AmitParan/smart-boiler/Matlab/figures/energy_philosophy.png

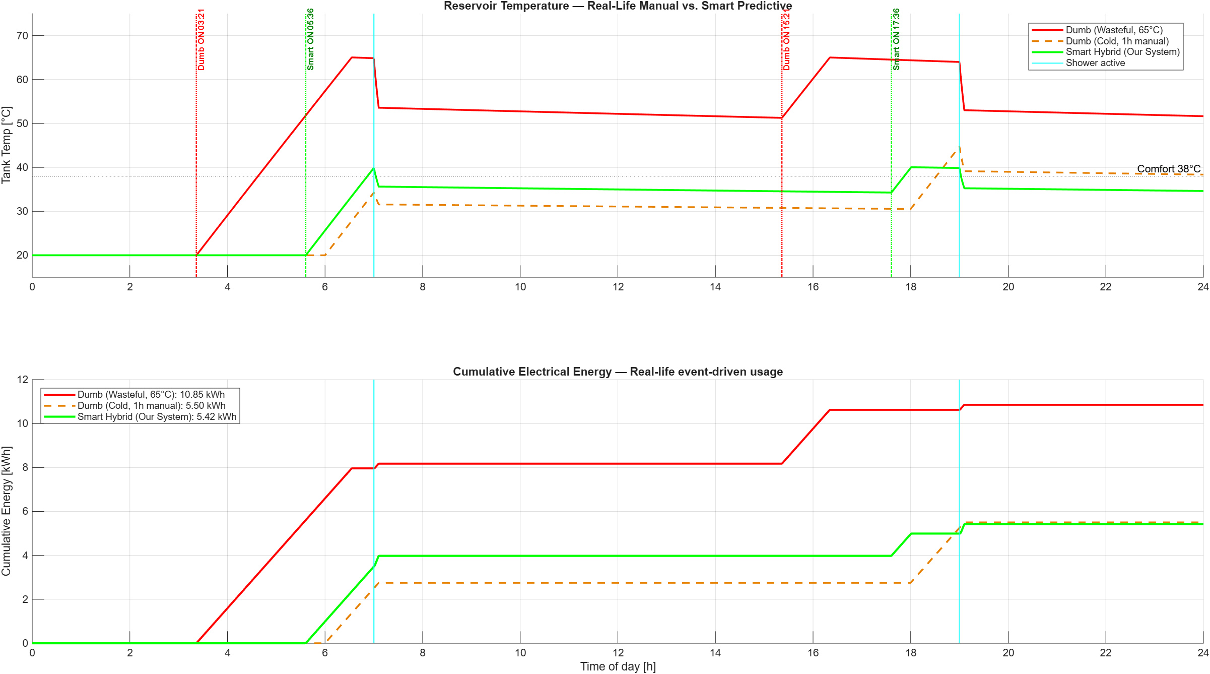
Matlab/figures/energy_philosophy.png
