AmitParan/smart-boiler/Matlab/figures/energy_stacked_breakdown.png

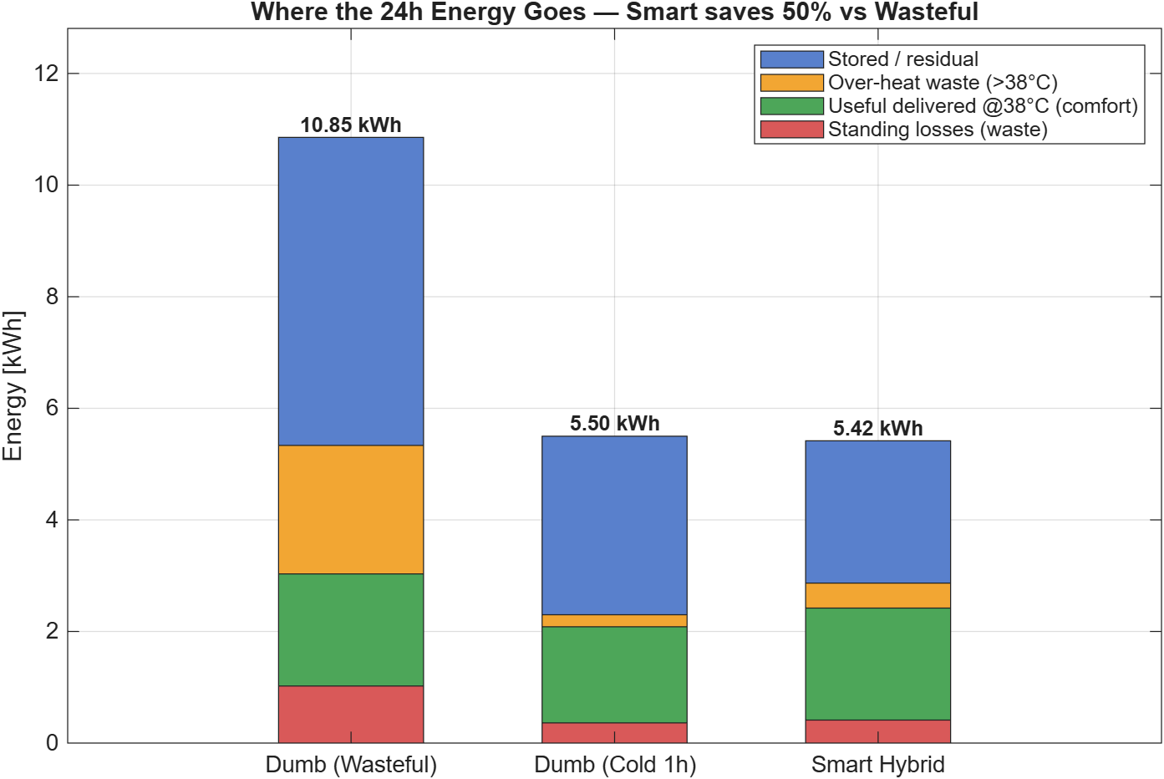
Matlab/figures/energy_stacked_breakdown.png
