AmitParan/smart-boiler/Matlab/figures/Scenario_1_Preheating.png

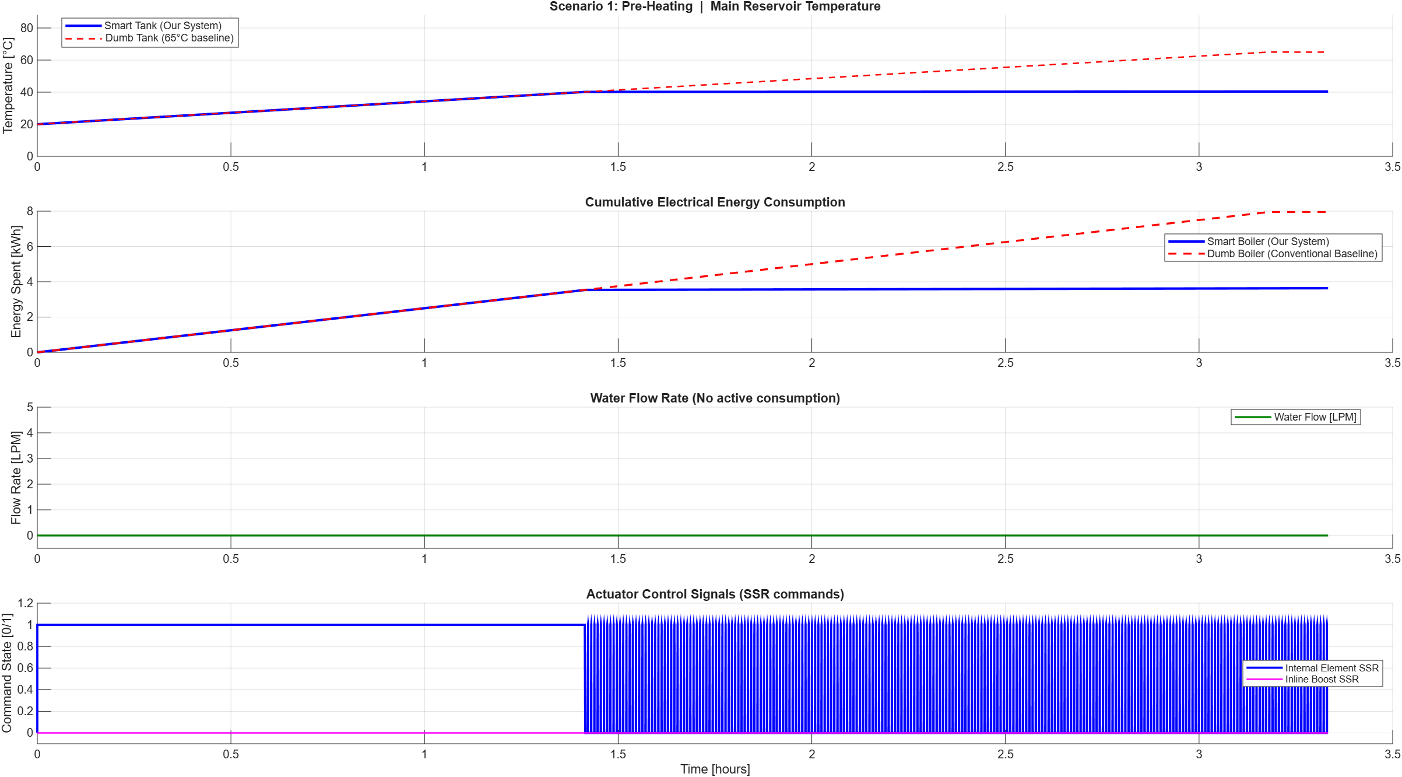
Matlab/figures/Scenario_1_Preheating.png
