AmitParan/smart-boiler/Matlab/figures/Scenario_2_ColdShowerStart.png

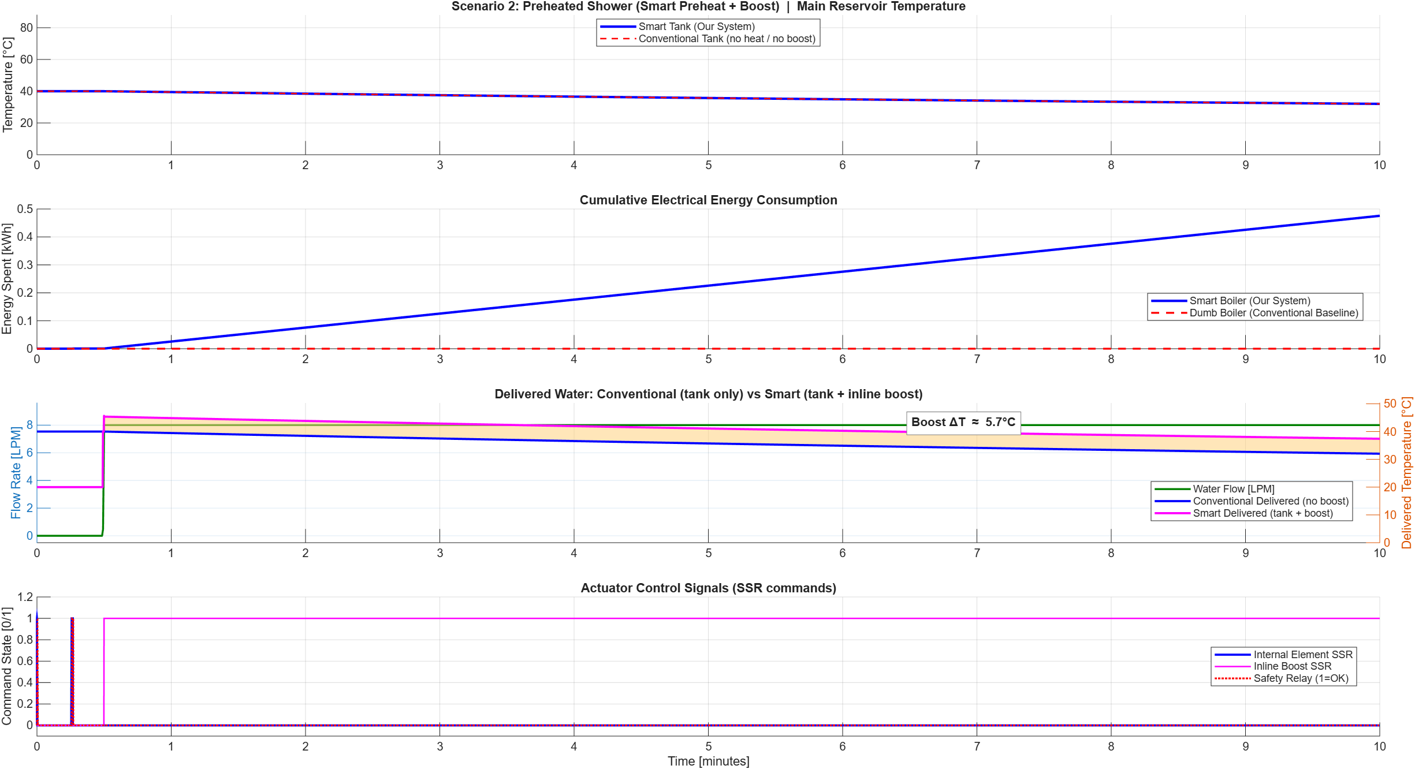
Matlab/figures/Scenario_2_ColdShowerStart.png
