AmitParan/smart-boiler/Matlab/figures/Scenario_5_SolarBypass.png

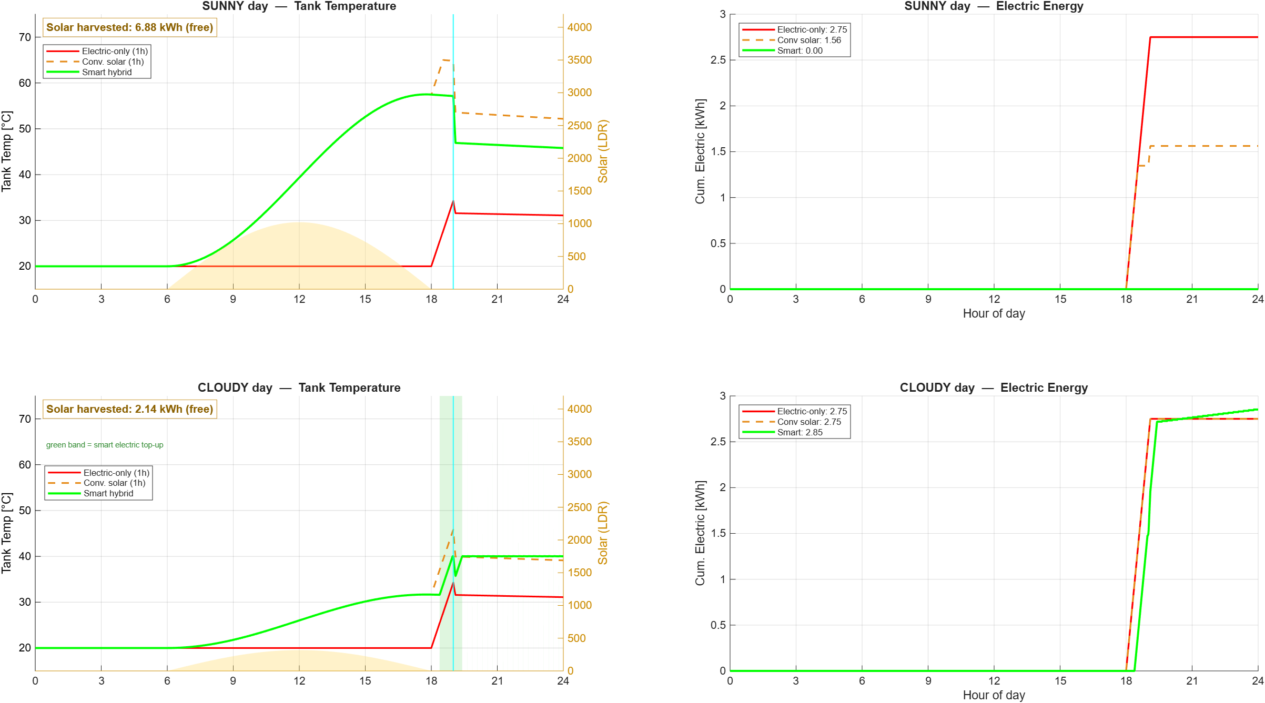
Matlab/figures/Scenario_5_SolarBypass.png
