AmitParan/smart-boiler/Matlab/figures/Scenario_6_PLC_CommLoss.png

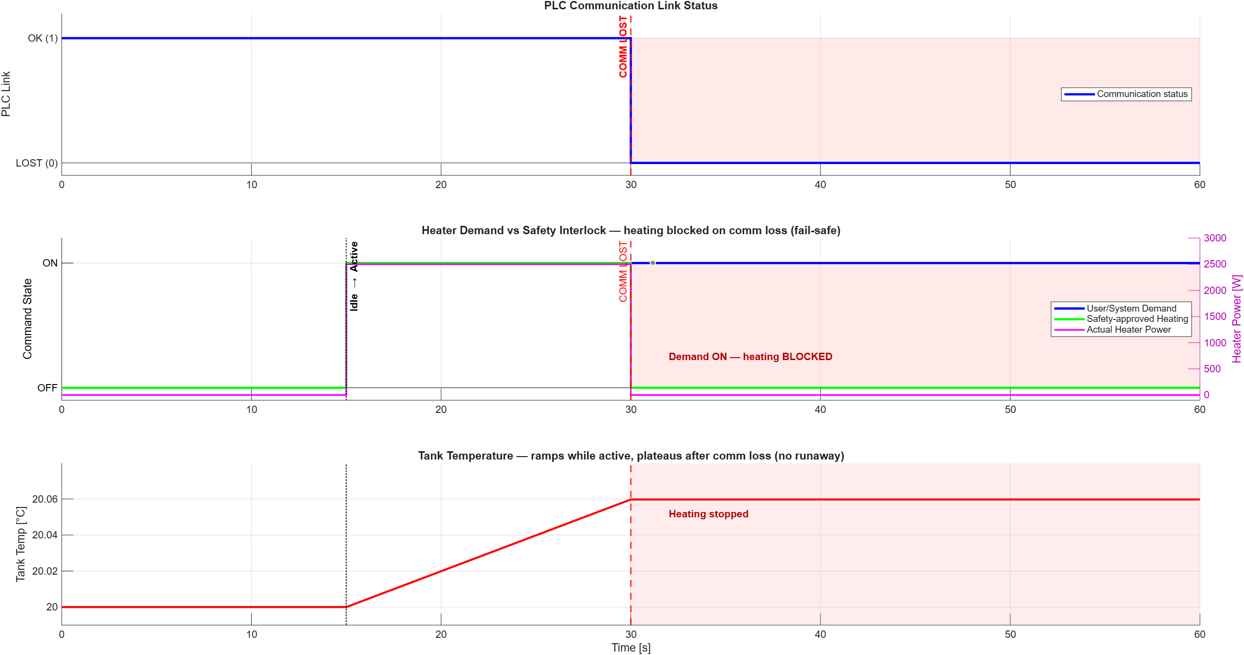
Matlab/figures/Scenario_6_PLC_CommLoss.png
