AmitParan/smart-boiler/slave/src/tasks/current_task.cpp

#include "current_task.h"
#include "config.h"
#include "shared_data.h"
#include "system_mode.h"
#include <Arduino.h>

static const int numSamples = 100;

void TaskCurrent(void * pvParameters) {
    // Initialize pin as analog first, then set attenuation
    analogReadResolution(12);
    analogRead(PIN_CURRENT_SENSOR);                              // primes the pin
    analogSetPinAttenuation(PIN_CURRENT_SENSOR, ADC_11db);

    // -----------------------------------------------------------------------
    //  Zero-current calibration
    //  SSRs are off at boot — average 200 samples to find the actual quiescent
    //  voltage of this specific sensor (ACS758 tolerance ±1% on VREF).
    // -----------------------------------------------------------------------
    Serial.println("[CURRENT] Calibrating zero reference...");
    float vref_sum = 0;
    for (int i = 0; i < 200; i++) {
        float v_adc = (analogRead(PIN_CURRENT_SENSOR) / 4095.0f) * 3.3f;
        vref_sum += v_adc / CURRENT_DIVIDER_RATIO;
        vTaskDelay(pdMS_TO_TICKS(5));
    }
    float vref_actual = vref_sum / 200.0f;

    // Derive actual VCC from measured VREF (ACS758: VREF = VCC/2)
    float vcc_actual = vref_actual * 2.0f;
    // Sensitivity scales linearly with VCC (spec is 40mV/A at 5V)
    float sensitivity_actual = ACS758_SENSITIVITY * (vcc_actual / 5.0f);

    Serial.printf("[CURRENT] Calibrated VREF = %.3fV (expected %.3fV)\n",
                  vref_actual, ACS758_VREF);
    Serial.printf("[CURRENT] VCC = %.3fV  sensitivity = %.1f mV/A (nominal 40.0)\n",
                  vcc_actual, sensitivity_actual * 1000.0f);

    // Validate VREF within ±10% of nominal 2.5V
    // If out of range the sensor is mis-powered — disable uncommanded-current check
    const float VREF_MIN = ACS758_VREF * 0.90f;  // 2.25V
    const float VREF_MAX = ACS758_VREF * 1.10f;  // 2.75V
    if (vref_actual >= VREF_MIN && vref_actual <= VREF_MAX) {
        current_sensor_valid = true;
        Serial.println("[CURRENT] Sensor OK — uncommanded-current check ENABLED");
    } else {
        current_sensor_valid = false;
        Serial.printf("[CURRENT] WARN: VREF out of range (%.3fV). Sensor mis-powered? Uncommanded-current check DISABLED.\n",
                      vref_actual);
    }
    Serial.println("[CURRENT] Task started");

    for(;;) {
        if (currentMode == MODE_DEMO) {
            // Compute mock RMS current from commanded SSR state
            uint8_t local_pwm_int = 0u, local_pwm_bst = 0u;
            if (xSemaphoreTake(guard_cmd, pdMS_TO_TICKS(10)) == pdTRUE) {
                local_pwm_int = cmd_pwm_internal;
                local_pwm_bst = cmd_pwm_boost;
                xSemaphoreGive(guard_cmd);
            }
            float mock_rms;
            if (slave_demo_fault_sim) {
                // Scenario 8: simulate stuck triac - report load even with cmds=0
                mock_rms = 13.64f;  // 3000W / 220V
            } else if (local_pwm_bst > 0u) {
                mock_rms = 13.64f;  // SSR BOOST (external) = 3000W / 220V
            } else if (local_pwm_int > 0u) {
                mock_rms = 11.36f;  // SSR INT (internal)   = 2500W / 220V
            } else {
                mock_rms = 0.0f;
            }
            if (xSemaphoreTake(guard_current, pdMS_TO_TICKS(10)) == pdTRUE) {
                current_rms = mock_rms;
                power_watts = mock_rms * 220.0f;
                xSemaphoreGive(guard_current);
            }
            vTaskDelay(pdMS_TO_TICKS(500));
            continue;
        }

        float sumSq = 0;

        // Sample the ADC to capture AC waveform (50 Hz)
        for (int i = 0; i < numSamples; i++) {
            float v_adc = (analogRead(PIN_CURRENT_SENSOR) / 4095.0f) * 3.3f;
            float v_sensor = v_adc / CURRENT_DIVIDER_RATIO;
            float current_instant = (v_sensor - vref_actual) / sensitivity_actual;
            sumSq += (current_instant * current_instant);
            vTaskDelay(pdMS_TO_TICKS(1));
        }

        float rms_current = sqrtf(sumSq / numSamples);

        // Filter noise floor
        if (rms_current < 0.2f) rms_current = 0.0f;

        if (xSemaphoreTake(guard_current, pdMS_TO_TICKS(10)) == pdTRUE) {
            current_rms = rms_current;
            power_watts = rms_current * 220.0f;
            xSemaphoreGive(guard_current);
        }

        vTaskDelay(pdMS_TO_TICKS(500));
    }
}
