AmitParan/smart-boiler/slave/src/core/shared_data.cpp

#include "shared_data.h"

// Sensor readings
float temps[3]       = {0.0f, 0.0f, 0.0f};
float current_flow   = 0.0f;
float current_rms    = 0.0f;
float power_watts    = 0.0f;

// SSR state flags
volatile bool    internal_ssr_on  = false;
volatile bool    boost_ssr_on     = false;

// Commands from master
volatile uint8_t cmd_pwm_internal = 0u;
volatile uint8_t cmd_pwm_boost    = 0u;
volatile uint8_t cmd_flags        = 0u;

// Safety
volatile bool    system_fault     = false;

// FreeRTOS mutexes (created in main.cpp setup(), before tasks start)
SemaphoreHandle_t guard_temps   = nullptr;
SemaphoreHandle_t guard_flow    = nullptr;
SemaphoreHandle_t guard_current = nullptr;
SemaphoreHandle_t guard_cmd     = nullptr;

// Demo mode flag-based sensor injection
volatile bool     slave_demo_flow_active = false;
volatile bool     slave_demo_overtemp    = false;
volatile bool     slave_demo_fault_sim   = false;

// PLC watchdog
volatile uint32_t last_cmd_received_ms = 0u;
volatile bool     cmd_ever_received    = false;
volatile bool     current_sensor_valid = false;  // set true only when VREF is in spec

// Temperature sensor health (REALTIME only) - see shared_data.h
volatile bool     temp_sensors_valid   = false;
volatile bool     temp_ever_read       = false;  // no REALTIME read attempted yet

// Spinlock for flow pulse counter ISR
portMUX_TYPE timerMux = portMUX_INITIALIZER_UNLOCKED;
