AmitParan/smart-boiler/slave/src/comms/plc_task.cpp

#include "plc_task.h"
#include "plc_comms.h"
#include "link.h"
#include "config.h"
#include <Arduino.h>

// ---------------------------------------------------------------------------
//  TaskPLC — triggered STATUS response + 5s heartbeat
//
//  Protocol (half-duplex KQ-330 — only one device transmits at a time):
//    1. Poll Serial1 every 10ms for incoming CMD from master
//    2. When CMD received: wait 200ms guard time, then push STATUS
//    3. Heartbeat: if no CMD received for 5s, push STATUS anyway so the
//       master knows the slave is alive
//
//  Why triggered instead of periodic unconditional push?
//  The KQ-330 is half-duplex. Master sends CMD every ~1s and listens for
//  STATUS for 3s. If slave also pushes every 1s independently, the two
//  transmissions collide on the power line and both packets are lost.
//  Triggered response guarantees the channel is quiet before slave TX.
// ---------------------------------------------------------------------------
void TaskPLC(void* pvParameters) {
    PLC_Init();
    Serial.printf("[COMMS] Task started over %s — triggered STATUS response\n",
                  link_name());

    uint32_t last_status_ms = millis();

    for (;;) {
        bool cmd_received = PLC_ReceivePacket();

        if (cmd_received) {
#ifndef LINK_WIFI
            // -----------------------------------------------------------------
            //  KQ-330 GUARD TIME — DO NOT CHANGE (PLC transport only)
            //  200ms is required between CMD receipt and STATUS transmission.
            //  This allows the KQ-330 power line carrier from the master's CMD
            //  to fully settle before the slave begins transmitting STATUS.
            //  Tested and verified at 200ms. Shorter values cause collisions.
            //
            //  WiFi needs none of this: UDP is full-duplex and there is no
            //  shared carrier to settle, so we answer immediately.
            // -----------------------------------------------------------------
            static const uint16_t KQ330_GUARD_TIME_MS = 200u;
            vTaskDelay(pdMS_TO_TICKS(KQ330_GUARD_TIME_MS));
#endif
            PLC_SendStatus();
            last_status_ms = millis();
        }

        // Heartbeat: push STATUS if master has been silent for 5 seconds
        if (millis() - last_status_ms >= 5000UL) {
            PLC_SendStatus();
            last_status_ms = millis();
        }

        vTaskDelay(pdMS_TO_TICKS(10));
    }
}
