AmitParan/smart-boiler/master/src/control/app_mode.h

#ifndef APP_MODE_H
#define APP_MODE_H

#include <Arduino.h>

// ---------------------------------------------------------------------------
//  AppMode — runtime operation mode (toggled from the Settings screen)
//
//  MODE_DEMO      : Master injects scripted sensor values into SystemManager.
//                       PLC is still active — slave receives real CMD packets
//                       and fires SSRs accordingly. Use this to demonstrate
//                       system behaviour or run automated test scenarios.
//
//  MODE_REALTIME  : Master uses actual sensor readings from slave STATUS
//                       packets. Normal production operation.
// ---------------------------------------------------------------------------
enum AppMode : uint8_t {
    MODE_DEMO     = 0,   ///< Automated scenarios; mock sensor data injected by master
    MODE_REALTIME = 1,   ///< Production; real sensors from slave STATUS packets
};

extern volatile AppMode appMode;

// ---------------------------------------------------------------------------
//  Demo mode injected values
//  Written by the demo scenario task, read by sendCommand() in comms_master.cpp.
// ---------------------------------------------------------------------------
extern volatile float demo_temp;    ///< tank temperature [°C]
extern volatile float demo_flow;    ///< flow rate [L/min]
extern volatile bool  demo_ui_on;   ///< boiler ON/OFF button state
extern volatile bool  demo_stop_comms;  ///< when true TaskMasterComms suppresses TX (scenario 6)
extern volatile bool  demo_fault_sim;   ///< when true slave simulates stuck-SSR current (scenario 8)
extern volatile bool  demo_solar_active; ///< when true scenario 5 solar sweep is running (changes log label)
#endif // APP_MODE_H
