AmitParan/smart-boiler/master/src/ui/ui_manager.cpp

// ui_manager.cpp  — Multi-screen consumer redesign (v6)
// Screen: 800 x 480  |  LVGL v8  |  Montserrat fonts
// Layout/flow ported from docs/ui-mockup/index.html

#include "ui_manager.h"
#include <Arduino.h>
#include "app_mode.h"
#include <WiFi.h>
#include <HTTPClient.h>
#include <ArduinoJson.h>
#include <esp_display_panel.hpp>
#include <lvgl.h>
#include <time.h>
#include "lvgl_v8_port.h"
#include "config.h"
#include "DataManager.h"

#define WEATHER_API_KEY      "7a1028898a2cdcc08a58a8109fb061e4"  // local only - do not commit
#define WEATHER_CITY         "Tel%20Aviv"  // URL-encoded space; a literal space breaks the request
#define WEATHER_COUNTRY_CODE "IL"
#define SETUP_AP_SSID        "Boiler-Setup"

using namespace esp_panel::drivers;
using namespace esp_panel::board;

// ---------------------------------------------------------------------------
//  Colour palette
// ---------------------------------------------------------------------------
#define CLR_BG       lv_color_hex(0xF0F4F8)  // light grey background
#define CLR_TOPBAR   lv_color_hex(0x1565C0)  // deep blue top bar / headers
#define CLR_ACCENT   lv_color_hex(0x1565C0)  // accent (buttons, ring)
#define CLR_ON       lv_color_hex(0x2E7D32)  // boiler ON  — green
#define CLR_OFF      lv_color_hex(0xC62828)  // boiler OFF — red
#define CLR_TEXT     lv_color_hex(0x1A1A2E)  // primary text
#define CLR_SUBTEXT  lv_color_hex(0x7B8794)  // secondary text
#define CLR_READY    lv_color_hex(0x2E7D32)  // shower ready
#define CLR_WAITING  lv_color_hex(0xE65100)  // shower not ready
#define CLR_BORDER   lv_color_hex(0xE0E0E0)  // card border
#define CLR_DIAG_BG  lv_color_hex(0x263238)  // diagnostics card background
#define CLR_DIAG_HDR lv_color_hex(0x37474F)  // diagnostics header background

static const int LEAD_TIME_MIN = 45;  // typical lead for the on-screen estimate only; the real lead is adaptive (smart_preheat.cpp)

// ---------------------------------------------------------------------------
//  Page containers (each 800x480, shown/hidden — only one visible at a time)
// ---------------------------------------------------------------------------
static lv_obj_t* page_home        = NULL;
static lv_obj_t* page_settings     = NULL;
static lv_obj_t* btn_app_mode      = NULL;  // Data-source (Demo/Real-time) button — Diagnostics header
static lv_obj_t* lbl_app_mode      = NULL;  // Data-source (Demo/Real-time) label — Diagnostics header
static lv_obj_t* page_schedule     = NULL;
static lv_obj_t* page_network      = NULL;
static lv_obj_t* page_password     = NULL;
static lv_obj_t* page_stats        = NULL;
static lv_obj_t* page_diagnostics  = NULL;
static lv_obj_t* page_solar        = NULL;
static lv_obj_t* page_wizard       = NULL;

// ---------------------------------------------------------------------------
//  Widget pointers — Home
// ---------------------------------------------------------------------------
lv_obj_t* lbl_water_temp     = NULL;
static lv_obj_t* lbl_target_inline = NULL;     // "Target 60°" inside the circle
lv_obj_t* lbl_time           = NULL;
lv_obj_t* lbl_date           = NULL;
lv_obj_t* btn_power          = NULL;
lv_obj_t* lbl_power_status   = NULL;
lv_obj_t* led_heating        = NULL;
lv_obj_t* lbl_wifi_icon      = NULL;
lv_obj_t* lbl_weather_icon   = NULL;
lv_obj_t* lbl_weather_temp   = NULL;
static lv_obj_t* temp_circle_obj      = NULL;
static lv_obj_t* lbl_shower_readiness = NULL;
static lv_obj_t* btn_auto_badge       = NULL;
static lv_obj_t* lbl_auto_badge       = NULL;

// Kept for header API compatibility
lv_obj_t* lbl_target_temp  = NULL;
lv_obj_t* btn_timer        = NULL;   // unused
lv_obj_t* lbl_timer_status = NULL;   // unused
lv_obj_t* btn_temp_up      = NULL;
lv_obj_t* btn_temp_down    = NULL;
lv_obj_t* lbl_boost_temp   = NULL;   // unused (no longer surfaced to consumer view)
lv_obj_t* lbl_flow_rate    = NULL;   // unused
lv_obj_t* lbl_showers      = NULL;   // unused
lv_obj_t* lbl_wait_time    = NULL;   // unused
lv_obj_t* lbl_system_mode  = NULL;   // shown on Stats page
lv_obj_t* led_ssr_internal = NULL;   // unused
lv_obj_t* led_ssr_boost    = NULL;   // unused

// ---------------------------------------------------------------------------
//  Widget pointers — Network / Password
// ---------------------------------------------------------------------------
static lv_obj_t* net_list_container = NULL;
static lv_obj_t* lbl_net_status     = NULL;
static lv_obj_t* lbl_pwd_title      = NULL;
static lv_obj_t* lbl_pwd_error      = NULL;
static lv_obj_t* password_textarea  = NULL;
static lv_obj_t* keyboard           = NULL;
static lv_obj_t* lbl_eye_icon       = NULL;
static lv_obj_t* btn_connect        = NULL;
static lv_obj_t* lbl_connect_btn_text = NULL;
static lv_obj_t* save_modal         = NULL;
static lv_obj_t* lbl_save_modal_ssid = NULL;

// ---------------------------------------------------------------------------
//  Widget pointers — Schedule
// ---------------------------------------------------------------------------
static lv_obj_t* sched_body         = NULL;
static lv_obj_t* btn_mode_manual    = NULL;
static lv_obj_t* lbl_mode_manual    = NULL;
static lv_obj_t* btn_mode_smart     = NULL;
static lv_obj_t* lbl_mode_smart     = NULL;
static lv_obj_t* btn_mode_ready     = NULL;
static lv_obj_t* lbl_mode_ready     = NULL;
static lv_obj_t* panel_ready        = NULL;
static lv_obj_t* panel_smart        = NULL;
static lv_obj_t* panel_manual       = NULL;
static lv_obj_t* sched_right_col    = NULL;
static lv_obj_t* btn_day_wk         = NULL;
static lv_obj_t* lbl_day_wk         = NULL;
static lv_obj_t* btn_day_we         = NULL;
static lv_obj_t* lbl_day_we         = NULL;
static lv_obj_t* btn_slot_am        = NULL;
static lv_obj_t* lbl_slot_am        = NULL;
static lv_obj_t* btn_slot_pm        = NULL;
static lv_obj_t* lbl_slot_pm        = NULL;
static lv_obj_t* btn_slot_en        = NULL;
static lv_obj_t* lbl_slot_en        = NULL;
static lv_obj_t* lbl_hh             = NULL;
static lv_obj_t* lbl_mm             = NULL;
static lv_obj_t* lbl_next_preheat   = NULL;
static lv_obj_t* lbl_skip_btn       = NULL;

// ---------------------------------------------------------------------------
//  Widget pointers — Setup Wizard (first-time preferences, Settings-triggered)
// ---------------------------------------------------------------------------
static lv_obj_t* wiz_step_temp      = NULL;
static lv_obj_t* wiz_step_household = NULL;
static lv_obj_t* wiz_step_schedule  = NULL;
static lv_obj_t* lbl_wiz_progress   = NULL;
static lv_obj_t* lbl_wiz_temp       = NULL;
static lv_obj_t* lbl_wiz_household  = NULL;
static lv_obj_t* lbl_wiz_hh         = NULL;
static lv_obj_t* lbl_wiz_mm         = NULL;
static lv_obj_t* btn_wiz_back       = NULL;
static lv_obj_t* btn_wiz_next       = NULL;
static lv_obj_t* lbl_wiz_next_text  = NULL;

// ---------------------------------------------------------------------------
//  Widget pointers — Stats (live status) / Diagnostics
// ---------------------------------------------------------------------------
static lv_obj_t* lbl_stat_power = NULL;
static lv_obj_t* lbl_stat_flow  = NULL;
static lv_obj_t* lbl_stat_plc   = NULL;
static lv_obj_t* lbl_usage_today = NULL;
static lv_obj_t* chart_usage     = NULL;
static lv_chart_series_t* ser_usage = NULL;

// ---------------------------------------------------------------------------
//  Widget pointers — Solar forecast page
// ---------------------------------------------------------------------------
static lv_obj_t* lbl_solar_peak  = NULL;
static lv_obj_t* chart_solar     = NULL;
static lv_chart_series_t* ser_solar = NULL;

static lv_obj_t* lbl_diag_tint   = NULL;
static lv_obj_t* lbl_diag_tboost = NULL;
static lv_obj_t* lbl_diag_flow   = NULL;
static lv_obj_t* lbl_diag_power  = NULL;
static lv_obj_t* lbl_diag_plc    = NULL;
static lv_obj_t* lbl_diag_heater_int   = NULL;
static lv_obj_t* lbl_diag_heater_boost = NULL;
static lv_obj_t* lbl_diag_rssi   = NULL;
static lv_obj_t* lbl_diag_heap   = NULL;
static lv_obj_t* lbl_diag_uptime = NULL;

// ---------------------------------------------------------------------------
//  Screensaver
// ---------------------------------------------------------------------------
static lv_obj_t* screensaver      = NULL;
static lv_obj_t* screensaver_time = NULL;
static lv_obj_t* screensaver_date = NULL;
unsigned long last_touch_time = 0;
#define SCREENSAVER_TIMEOUT 60000

// ---------------------------------------------------------------------------
//  State
// ---------------------------------------------------------------------------
bool   boiler_state       = false;
bool   timer_enabled      = false;
int    target_temperature = 60;
bool   wifi_connected     = false;
char   selected_network[64] = "";
String scanned_networks[20];
int    scanned_rssi[20];
int    num_networks         = 0;
unsigned long last_weather_update = 0;

// Water usage tracking (Stats page) — 24 hourly buckets, reset at midnight,
// persisted to flash so a reboot doesn't lose today's progress.
#define USAGE_HOURS 24
static float g_hourly_liters[USAGE_HOURS] = {0};
static float g_hourly_temp[USAGE_HOURS]   = {0};
static int   g_usage_day             = -1;   // day-of-year; -1 = not loaded yet
static unsigned long g_last_usage_ms      = 0;
static unsigned long g_last_usage_save_ms = 0;

// Schedule — operation-mode + ready-by state. Drives the SmartPreheat brain
// (smart_preheat.cpp) via UI_GetOpMode() / UI_GetReadyByMinutes().
static bool g_auto_enabled  = true;
static bool g_smart_learn   = false;   // false = "Ready by" mode
// Ready-by schedule: [day-type][slot]. day 0=weekday 1=weekend, slot 0=morning 1=evening.
static int  g_ready_hh[2][2] = {{7, 19}, {9, 19}};
static int  g_ready_mm[2][2] = {{0, 0},  {0, 0}};
static bool g_ready_en[2][2] = {{true, false}, {true, false}};  // is this slot active?
static int  g_sched_day_idx  = 0;   // which day-type is being edited (0=weekday 1=weekend)
static int  g_sched_slot_idx = 0;   // which slot is being edited   (0=morning 1=evening)
static bool g_skip_today     = false;

// Setup Wizard — working values for the in-progress step, plus the last
// persisted household/ready-time preferences (loaded at boot, used to
// prefill the wizard next time it's opened). target_temperature doubles
// as both the live value and the persisted preference, so it isn't
// duplicated here.
static int  wizard_step      = 0;   // 0..2
static int  wiz_temp         = 60;
static int  wiz_household    = 2;
static int  wiz_ready_hh     = 7;
static int  wiz_ready_mm     = 0;
static int  g_pref_household = 2;
static int  g_pref_ready_hh  = 7;
static int  g_pref_ready_mm  = 0;

// ---------------------------------------------------------------------------
//  Smart-preheat interface — exposes the Schedule-page operation state to the
//  SmartPreheat brain (smart_preheat.cpp), so the three UI modes drive real
//  heating behaviour instead of being a front-end placeholder.
// ---------------------------------------------------------------------------
#include <time.h>

uint8_t UI_GetOpMode() {
    if (!g_auto_enabled) return 0;        // OP_DUMB — auto disabled (plain reactive)
    return g_smart_learn ? 2 : 1;         // OP_SMART : OP_READY_BY
}

uint8_t UI_GetReadyByMinutes(uint16_t* out, uint8_t maxN) {
    // Enabled ready-by times for today (Israel weekend = Fri/Sat). Falls back to
    // the weekday set when the clock is not synced yet. Returns how many filled.
    int idx = 0;
    time_t now = time(nullptr);
    if (now > 100000) {
        struct tm tmv;
        localtime_r(&now, &tmv);
        if (tmv.tm_wday == 5 || tmv.tm_wday == 6) idx = 1;
    }
    uint8_t n = 0;
    for (int s = 0; s < 2 && n < maxN; s++) {
        if (g_ready_en[idx][s]) out[n++] = (uint16_t)(g_ready_hh[idx][s] * 60 + g_ready_mm[idx][s]);
    }
    return n;
}

uint8_t UI_GetHouseholdSize() {
    return (uint8_t)g_pref_household;
}

// ---------------------------------------------------------------------------
//  Helpers
// ---------------------------------------------------------------------------
static bool stationConnected() { return WiFi.status() == WL_CONNECTED; }

static void disableScroll(lv_obj_t* obj) {
    if (obj == NULL) return;
    lv_obj_clear_flag(obj, LV_OBJ_FLAG_SCROLLABLE);
    lv_obj_set_scrollbar_mode(obj, LV_SCROLLBAR_MODE_OFF);
}

static void restoreSetupApIfNeeded() {
    WiFi.mode(WIFI_AP_STA);
    if (WiFi.softAPSSID() != String(SETUP_AP_SSID))
        WiFi.softAP(SETUP_AP_SSID, "12345678");
}

static int performWifiScan() {
    WiFi.scanDelete();
    WiFi.setSleep(false);
    WiFi.disconnect(false, true);
    WiFi.mode(WIFI_OFF);
    delay(250);
    WiFi.mode(WIFI_STA);
    delay(750);
    int found = WiFi.scanNetworks(false, true);
    Serial.printf("WiFi scan result: %d\n", found);
    return found;
}

static int scanForNetworks() {
    bool   was_connected = stationConnected();
    String cur_ssid      = was_connected ? WiFi.SSID() : String();
    String cur_psk       = was_connected ? WiFi.psk()  : String();

    int found = performWifiScan();
    if (found < 0) found = performWifiScan();

    // Capture results now, before the mode switch below invalidates the
    // scan cache (WiFi.mode()/WiFi.begin() clears WiFi.SSID(i)/RSSI(i)).
    for (int i = 0; i < found && i < 20; i++) {
        scanned_networks[i] = WiFi.SSID(i);
        scanned_rssi[i]     = WiFi.RSSI(i);
    }

    if (was_connected) {
        WiFi.mode(WIFI_STA);
        WiFi.begin(cur_ssid.c_str(), cur_psk.c_str());
        int timeout = 10; // up to ~5s, matches attempt_wifi_connect()'s pacing
        while (WiFi.status() != WL_CONNECTED && timeout-- > 0) delay(500);
    } else {
        restoreSetupApIfNeeded();
    }
    return found;
}

// ---------------------------------------------------------------------------
//  Page navigation
// ---------------------------------------------------------------------------
static void show_page(lv_obj_t* target) {
    lv_obj_t* pages[] = { page_home, page_settings, page_schedule, page_network,
                          page_password, page_stats, page_diagnostics, page_solar,
                          page_wizard };
    for (lv_obj_t* p : pages) {
        if (p == NULL) continue;
        if (p == target) lv_obj_clear_flag(p, LV_OBJ_FLAG_HIDDEN);
        else              lv_obj_add_flag(p, LV_OBJ_FLAG_HIDDEN);
    }
    last_touch_time = millis();
}

static void nav_back_cb(lv_event_t* e) {
    last_touch_time = millis();
    lv_obj_t* target = (lv_obj_t*)lv_event_get_user_data(e);
    show_page(target);
}

// ---------------------------------------------------------------------------
//  Touch / screensaver
// ---------------------------------------------------------------------------
static void screen_touched_cb(lv_event_t* e) {
    last_touch_time = millis();
    if (screensaver != NULL && lv_obj_is_visible(screensaver))
        lv_obj_add_flag(screensaver, LV_OBJ_FLAG_HIDDEN);
}

// ---------------------------------------------------------------------------
//  Reusable component helpers
// ---------------------------------------------------------------------------
static lv_obj_t* make_header(lv_obj_t* parent, lv_color_t bg) {
    lv_obj_t* header = lv_obj_create(parent);
    disableScroll(header);
    lv_obj_set_size(header, 800, 64);
    lv_obj_set_pos(header, 0, 0);
    lv_obj_set_style_bg_color(header, bg, 0);
    lv_obj_set_style_border_width(header, 0, 0);
    lv_obj_set_style_radius(header, 0, 0);
    lv_obj_set_style_pad_hor(header, 12, 0);
    lv_obj_set_style_pad_ver(header, 0, 0);
    lv_obj_set_style_pad_column(header, 12, 0);
    lv_obj_set_flex_flow(header, LV_FLEX_FLOW_ROW);
    lv_obj_set_flex_align(header, LV_FLEX_ALIGN_START, LV_FLEX_ALIGN_CENTER, LV_FLEX_ALIGN_CENTER);
    return header;
}

static lv_obj_t* make_back_btn(lv_obj_t* header, lv_obj_t* target_page) {
    lv_obj_t* btn = lv_btn_create(header);
    lv_obj_set_size(btn, 64, 48);
    lv_obj_set_style_radius(btn, 12, 0);
    lv_obj_set_style_bg_color(btn, lv_color_white(), 0);
    lv_obj_set_style_bg_opa(btn, LV_OPA_20, 0);
    lv_obj_set_style_border_width(btn, 0, 0);
    lv_obj_add_event_cb(btn, nav_back_cb, LV_EVENT_CLICKED, target_page);
    lv_obj_t* lbl = lv_label_create(btn);
    lv_label_set_text(lbl, LV_SYMBOL_LEFT);
    lv_obj_set_style_text_font(lbl, &lv_font_montserrat_22, 0);
    lv_obj_set_style_text_color(lbl, lv_color_white(), 0);
    lv_obj_center(lbl);
    return btn;
}

static lv_obj_t* make_header_title(lv_obj_t* header, const char* text) {
    lv_obj_t* lbl = lv_label_create(header);
    lv_label_set_text(lbl, text);
    lv_obj_set_style_text_font(lbl, &lv_font_montserrat_24, 0);
    lv_obj_set_style_text_color(lbl, lv_color_white(), 0);
    lv_obj_set_flex_grow(lbl, 1);
    return lbl;
}

// Small up/value/down column, e.g. household size or one half of a HH:MM
// picker. Mirrors the stepper built inline in build_schedule_page().
static lv_obj_t* make_value_stepper(lv_obj_t* parent, lv_event_cb_t up_cb, lv_event_cb_t dn_cb, lv_obj_t** out_lbl) {
    lv_obj_t* col = lv_obj_create(parent);
    disableScroll(col);
    lv_obj_set_size(col, 70, 120);
    lv_obj_set_style_bg_opa(col, LV_OPA_TRANSP, 0);
    lv_obj_set_style_border_width(col, 0, 0);
    lv_obj_set_style_pad_all(col, 0, 0);
    lv_obj_set_flex_flow(col, LV_FLEX_FLOW_COLUMN);
    lv_obj_set_flex_align(col, LV_FLEX_ALIGN_SPACE_BETWEEN, LV_FLEX_ALIGN_CENTER, LV_FLEX_ALIGN_CENTER);

    lv_obj_t* up = lv_btn_create(col);
    lv_obj_set_size(up, 64, 40);
    lv_obj_set_style_radius(up, 12, 0);
    lv_obj_set_style_bg_color(up, lv_color_hex(0xE3F2FD), 0);
    lv_obj_set_style_shadow_width(up, 0, 0);
    lv_obj_add_event_cb(up, up_cb, LV_EVENT_CLICKED, NULL);
    lv_obj_t* up_lbl = lv_label_create(up);
    lv_label_set_text(up_lbl, LV_SYMBOL_UP);
    lv_obj_set_style_text_color(up_lbl, CLR_ACCENT, 0);
    lv_obj_center(up_lbl);

    lv_obj_t* val = lv_label_create(col);
    lv_label_set_text(val, "00");
    lv_obj_set_style_text_font(val, &lv_font_montserrat_48, 0);
    if (out_lbl) *out_lbl = val;

    lv_obj_t* dn = lv_btn_create(col);
    lv_obj_set_size(dn, 64, 40);
    lv_obj_set_style_radius(dn, 12, 0);
    lv_obj_set_style_bg_color(dn, lv_color_hex(0xE3F2FD), 0);
    lv_obj_set_style_shadow_width(dn, 0, 0);
    lv_obj_add_event_cb(dn, dn_cb, LV_EVENT_CLICKED, NULL);
    lv_obj_t* dn_lbl = lv_label_create(dn);
    lv_label_set_text(dn_lbl, LV_SYMBOL_DOWN);
    lv_obj_set_style_text_color(dn_lbl, CLR_ACCENT, 0);
    lv_obj_center(dn_lbl);
    return col;
}

static lv_obj_t* make_tile(lv_obj_t* parent, const char* icon, const char* text,
                            lv_color_t bg, lv_color_t border, lv_color_t fg,
                            lv_event_cb_t cb) {
    lv_obj_t* tile = lv_btn_create(parent);
    disableScroll(tile);
    lv_obj_set_flex_grow(tile, 1);
    lv_obj_set_height(tile, 116);
    lv_obj_set_style_radius(tile, 22, 0);
    lv_obj_set_style_bg_color(tile, bg, 0);
    lv_obj_set_style_border_width(tile, 2, 0);
    lv_obj_set_style_border_color(tile, border, 0);
    lv_obj_set_style_shadow_width(tile, 0, 0);
    lv_obj_set_flex_flow(tile, LV_FLEX_FLOW_COLUMN);
    lv_obj_set_flex_align(tile, LV_FLEX_ALIGN_CENTER, LV_FLEX_ALIGN_CENTER, LV_FLEX_ALIGN_CENTER);
    lv_obj_set_style_pad_row(tile, 8, 0);
    if (cb) lv_obj_add_event_cb(tile, cb, LV_EVENT_CLICKED, NULL);

    lv_obj_t* lbl_icon = lv_label_create(tile);
    lv_label_set_text(lbl_icon, icon);
    lv_obj_set_style_text_font(lbl_icon, &lv_font_montserrat_32, 0);
    lv_obj_set_style_text_color(lbl_icon, fg, 0);

    lv_obj_t* lbl_text = lv_label_create(tile);
    lv_label_set_text(lbl_text, text);
    lv_obj_set_style_text_font(lbl_text, &lv_font_montserrat_20, 0);
    lv_obj_set_style_text_color(lbl_text, fg, 0);
    return tile;
}

// Small stat card used on the Stats page: title + big value label (returned)
static lv_obj_t* make_stat_card(lv_obj_t* parent, const char* title, lv_color_t value_color) {
    lv_obj_t* card = lv_obj_create(parent);
    disableScroll(card);
    lv_obj_set_flex_grow(card, 1);
    lv_obj_set_height(card, 90);
    lv_obj_set_style_radius(card, 16, 0);
    lv_obj_set_style_bg_color(card, lv_color_white(), 0);
    lv_obj_set_style_border_width(card, 2, 0);
    lv_obj_set_style_border_color(card, CLR_BORDER, 0);
    lv_obj_set_style_pad_all(card, 12, 0);

    lv_obj_t* lbl_title = lv_label_create(card);
    lv_label_set_text(lbl_title, title);
    lv_obj_set_style_text_font(lbl_title, &lv_font_montserrat_14, 0);
    lv_obj_set_style_text_color(lbl_title, CLR_SUBTEXT, 0);
    lv_obj_align(lbl_title, LV_ALIGN_TOP_LEFT, 0, 0);

    lv_obj_t* lbl_value = lv_label_create(card);
    lv_label_set_text(lbl_value, "--");
    lv_obj_set_style_text_font(lbl_value, &lv_font_montserrat_28, 0);
    lv_obj_set_style_text_color(lbl_value, value_color, 0);
    lv_obj_align(lbl_value, LV_ALIGN_BOTTOM_LEFT, 0, 0);
    return lbl_value;
}

// Dark diagnostics card: title + value label (returned)
static lv_obj_t* make_diag_card(lv_obj_t* parent, const char* title, lv_color_t value_color) {
    lv_obj_t* card = lv_obj_create(parent);
    disableScroll(card);
    lv_obj_set_style_bg_color(card, CLR_DIAG_BG, 0);
    lv_obj_set_style_radius(card, 12, 0);
    lv_obj_set_style_border_width(card, 0, 0);
    lv_obj_set_style_pad_all(card, 14, 0);

    lv_obj_t* lbl_title = lv_label_create(card);
    lv_label_set_text(lbl_title, title);
    lv_obj_set_style_text_font(lbl_title, &lv_font_montserrat_14, 0);
    lv_obj_set_style_text_color(lbl_title, lv_color_hex(0xB0BEC5), 0);
    lv_obj_align(lbl_title, LV_ALIGN_TOP_LEFT, 0, 0);

    lv_obj_t* lbl_value = lv_label_create(card);
    lv_label_set_text(lbl_value, "--");
    lv_obj_set_style_text_font(lbl_value, &lv_font_montserrat_22, 0);
    lv_obj_set_style_text_color(lbl_value, value_color, 0);
    lv_obj_align(lbl_value, LV_ALIGN_BOTTOM_LEFT, 0, 0);
    return lbl_value;
}

// ---------------------------------------------------------------------------
//  Target temperature (shared between Home circle subtitle and Settings)
// ---------------------------------------------------------------------------
static void updateTargetLabels() {
    char buf[8];
    snprintf(buf, sizeof(buf), "%d\xc2\xb0", target_temperature);
    if (lbl_target_temp != NULL) lv_label_set_text(lbl_target_temp, buf);
    if (lbl_target_inline != NULL) {
        char buf2[20];
        snprintf(buf2, sizeof(buf2), "Target %d\xc2\xb0", target_temperature);
        lv_label_set_text(lbl_target_inline, buf2);
    }
}

static void power_btn_event_cb(lv_event_t* e) {
    last_touch_time = millis();
    if (appMode == MODE_DEMO) return;
    boiler_state = !boiler_state;
    if (btn_power        != NULL) lv_obj_set_style_bg_color(btn_power, boiler_state ? CLR_ON : CLR_OFF, 0);
    if (lbl_power_status != NULL) lv_label_set_text(lbl_power_status, boiler_state ? "ON" : "OFF");
    Serial.printf("Boiler: %s\n", boiler_state ? "ON" : "OFF");
}

static void temp_up_btn_event_cb(lv_event_t* e) {
    last_touch_time = millis();
    if (target_temperature < 65) {
        target_temperature += 5;
        updateTargetLabels();
    }
}

static void temp_down_btn_event_cb(lv_event_t* e) {
    last_touch_time = millis();
    if (target_temperature > 25) {
        target_temperature -= 5;
        updateTargetLabels();
    }
}

// ---------------------------------------------------------------------------
//  Network / Password flow
//  Key change from v5: the "save password" checkbox is gone. Instead we ask
//  "Save this password?" only AFTER a successful connect.
// ---------------------------------------------------------------------------
static void refresh_network_status() {
    if (lbl_net_status == NULL) return;
    if (WiFi.status() == WL_CONNECTED) {
        char buf[64];
        snprintf(buf, sizeof(buf), LV_SYMBOL_OK "  Connected to %s", WiFi.SSID().c_str());
        lv_label_set_text(lbl_net_status, buf);
        lv_obj_set_style_text_color(lbl_net_status, lv_palette_main(LV_PALETTE_GREEN), 0);
    } else {
        lv_label_set_text(lbl_net_status, LV_SYMBOL_WARNING "  Not connected");
        lv_obj_set_style_text_color(lbl_net_status, lv_palette_main(LV_PALETTE_RED), 0);
    }
}

static void net_row_click_cb(lv_event_t* e);

static void rebuild_network_list() {
    if (net_list_container == NULL) return;
    lv_obj_clean(net_list_container);

    num_networks = scanForNetworks();

    if (num_networks <= 0) {
        lv_obj_t* lbl = lv_label_create(net_list_container);
        lv_label_set_text(lbl, (num_networks == 0) ? "No networks found" : "Scan failed");
        lv_obj_set_style_text_font(lbl, &lv_font_montserrat_18, 0);
        lv_obj_set_style_text_color(lbl, CLR_SUBTEXT, 0);
        return;
    }

    for (int i = 0; i < num_networks && i < 20; i++) {
        lv_obj_t* row = lv_btn_create(net_list_container);
        disableScroll(row);
        lv_obj_set_size(row, lv_pct(100), 64);
        lv_obj_set_style_radius(row, 16, 0);
        lv_obj_set_style_bg_color(row, lv_color_white(), 0);
        lv_obj_set_style_border_width(row, 2, 0);
        lv_obj_set_style_border_color(row, CLR_BORDER, 0);
        lv_obj_set_style_shadow_width(row, 0, 0);
        lv_obj_set_flex_flow(row, LV_FLEX_FLOW_ROW);
        lv_obj_set_flex_align(row, LV_FLEX_ALIGN_START, LV_FLEX_ALIGN_CENTER, LV_FLEX_ALIGN_CENTER);
        lv_obj_set_style_pad_column(row, 14, 0);
        lv_obj_set_style_pad_hor(row, 18, 0);
        lv_obj_add_event_cb(row, net_row_click_cb, LV_EVENT_CLICKED, (void*)scanned_networks[i].c_str());

        lv_obj_t* icon = lv_label_create(row);
        lv_label_set_text(icon, LV_SYMBOL_WIFI);
        lv_obj_set_style_text_font(icon, &lv_font_montserrat_22, 0);
        lv_obj_set_style_text_color(icon, CLR_ACCENT, 0);

        lv_obj_t* name = lv_label_create(row);
        lv_label_set_text(name, scanned_networks[i].c_str());
        lv_obj_set_style_text_font(name, &lv_font_montserrat_20, 0);
        lv_obj_set_style_text_color(name, CLR_TEXT, 0);
        lv_obj_set_flex_grow(name, 1);

        lv_obj_t* rssi = lv_label_create(row);
        char rbuf[16];
        snprintf(rbuf, sizeof(rbuf), "%d dBm", scanned_rssi[i]);
        lv_label_set_text(rssi, rbuf);
        lv_obj_set_style_text_font(rssi, &lv_font_montserrat_14, 0);
        lv_obj_set_style_text_color(rssi, CLR_SUBTEXT, 0);
    }
}

static void net_scan_btn_cb(lv_event_t* e) {
    last_touch_time = millis();
    rebuild_network_list();
}

static void open_password_page(const char* ssid) {
    last_touch_time = millis();
    strncpy(selected_network, ssid, sizeof(selected_network) - 1);
    selected_network[sizeof(selected_network) - 1] = '\0';

    if (lbl_pwd_title     != NULL) lv_label_set_text(lbl_pwd_title, selected_network);
    if (password_textarea != NULL) {
        lv_textarea_set_text(password_textarea, "");
        lv_textarea_set_password_mode(password_textarea, true);
    }
    if (lbl_eye_icon != NULL) lv_label_set_text(lbl_eye_icon, LV_SYMBOL_EYE_CLOSE);
    if (lbl_pwd_error != NULL) lv_label_set_text(lbl_pwd_error, "");
    show_page(page_password);
}

static void net_row_click_cb(lv_event_t* e) {
    const char* ssid = (const char*)lv_event_get_user_data(e);
    open_password_page(ssid);
}

static void goto_network_cb(lv_event_t* e) {
    last_touch_time = millis();
    show_page(page_network);
    rebuild_network_list();
    refresh_network_status();
}

static void pwd_eye_toggle_cb(lv_event_t* e) {
    last_touch_time = millis();
    if (password_textarea == NULL) return;
    bool was_hidden = lv_textarea_get_password_mode(password_textarea);
    lv_textarea_set_password_mode(password_textarea, !was_hidden);
    if (lbl_eye_icon != NULL)
        lv_label_set_text(lbl_eye_icon, was_hidden ? LV_SYMBOL_EYE_OPEN : LV_SYMBOL_EYE_CLOSE);
}

static bool attempt_wifi_connect(const char* ssid, const char* password) {
    if (WiFi.status() == WL_CONNECTED) { WiFi.disconnect(true, true); delay(100); }
    WiFi.mode(WIFI_AP_STA);
    WiFi.begin(ssid, password);
    int timeout = 20;
    while (WiFi.status() != WL_CONNECTED && timeout-- > 0) delay(500);
    if (WiFi.status() == WL_CONNECTED) {
        WiFi.softAPdisconnect(true);
        return true;
    }
    WiFi.mode(WIFI_AP_STA);
    if (WiFi.softAPSSID() != String(SETUP_AP_SSID)) WiFi.softAP(SETUP_AP_SSID, "12345678");
    return false;
}

static void pwd_connect_btn_cb(lv_event_t* e) {
    last_touch_time = millis();
    if (password_textarea == NULL) return;
    const char* password = lv_textarea_get_text(password_textarea);

    if (lbl_connect_btn_text != NULL) lv_label_set_text(lbl_connect_btn_text, "Connecting...");
    if (btn_connect          != NULL) lv_obj_set_style_bg_color(btn_connect, lv_palette_main(LV_PALETTE_GREY), 0);
    lv_refr_now(NULL);

    bool ok = attempt_wifi_connect(selected_network, password);

    if (ok) {
        wifi_connected = true;
        if (lbl_wifi_icon != NULL) lv_obj_set_style_text_color(lbl_wifi_icon, lv_palette_main(LV_PALETTE_GREEN), 0);
        if (lbl_pwd_error != NULL) lv_label_set_text(lbl_pwd_error, "");
        if (lbl_save_modal_ssid != NULL) lv_label_set_text(lbl_save_modal_ssid, selected_network);
        if (save_modal != NULL) lv_obj_clear_flag(save_modal, LV_OBJ_FLAG_HIDDEN);
    } else {
        wifi_connected = false;
        if (lbl_wifi_icon != NULL) lv_obj_set_style_text_color(lbl_wifi_icon, lv_palette_main(LV_PALETTE_RED), 0);
        if (lbl_pwd_error != NULL) lv_label_set_text(lbl_pwd_error, "Couldn't connect. Check the password and try again.");
    }

    if (lbl_connect_btn_text != NULL) lv_label_set_text(lbl_connect_btn_text, "Connect");
    if (btn_connect          != NULL) lv_obj_set_style_bg_color(btn_connect, CLR_ON, 0);
}

static void save_modal_close(bool save_password) {
    if (save_password) DataManager::saveWiFiCredentials(selected_network, lv_textarea_get_text(password_textarea));
    if (save_modal != NULL) lv_obj_add_flag(save_modal, LV_OBJ_FLAG_HIDDEN);
    refresh_network_status();
    show_page(page_network);
}

static void save_modal_yes_cb(lv_event_t* e) { last_touch_time = millis(); save_modal_close(true); }
static void save_modal_no_cb(lv_event_t* e)  { last_touch_time = millis(); save_modal_close(false); }

static void wifi_icon_click_event_cb(lv_event_t* e) { goto_network_cb(e); }

// ---------------------------------------------------------------------------
//  Schedule (local UI state only — see note at g_auto_enabled declaration)
// ---------------------------------------------------------------------------
// Earliest enabled ready-by time (minute-of-day) for a day-type, or -1 if none.
static int earliest_ready(int day) {
    int best = -1;
    for (int s = 0; s < 2; s++) {
        if (g_ready_en[day][s]) {
            int t = g_ready_hh[day][s] * 60 + g_ready_mm[day][s];
            if (best < 0 || t < best) best = t;
        }
    }
    return best;
}

static void update_auto_badge() {
    if (btn_auto_badge == NULL || lbl_auto_badge == NULL) return;
    if (!g_auto_enabled) {
        lv_obj_set_style_bg_color(btn_auto_badge, lv_palette_main(LV_PALETTE_GREY), 0);
        lv_label_set_text(lbl_auto_badge, LV_SYMBOL_CHARGE "  Manual");
        return;
    }
    lv_obj_set_style_bg_color(btn_auto_badge, lv_palette_main(LV_PALETTE_GREEN), 0);
    if (g_smart_learn) {
        lv_label_set_text(lbl_auto_badge, LV_SYMBOL_CHARGE "  Auto (smart)");
        return;
    }
    int r = earliest_ready(g_sched_day_idx);
    if (r < 0) { lv_label_set_text(lbl_auto_badge, LV_SYMBOL_CHARGE "  Auto --:--"); return; }
    int total = r - LEAD_TIME_MIN;
    if (total < 0) total += 1440;
    char buf[24];
    snprintf(buf, sizeof(buf), LV_SYMBOL_CHARGE "  Auto %02d:%02d", total / 60, total % 60);
    lv_label_set_text(lbl_auto_badge, buf);
}

static void recompute_next_preheat() {
    if (lbl_next_preheat != NULL) {
        int r = earliest_ready(g_sched_day_idx);
        if (r < 0) {
            lv_label_set_text(lbl_next_preheat, "--:--");
        } else {
            int total = r - LEAD_TIME_MIN;
            if (total < 0) total += 1440;
            char buf[8];
            snprintf(buf, sizeof(buf), "%02d:%02d", total / 60, total % 60);
            lv_label_set_text(lbl_next_preheat, buf);
        }
    }
    update_auto_badge();
}

// Highlights the Morning/Evening slot selector + the current slot's On/Off toggle.
static void update_slot_buttons() {
    bool am = (g_sched_slot_idx == 0);
    if (btn_slot_am != NULL) lv_obj_set_style_bg_color(btn_slot_am, am ? CLR_ACCENT : lv_color_white(), 0);
    if (lbl_slot_am != NULL) lv_obj_set_style_text_color(lbl_slot_am, am ? lv_color_white() : CLR_TEXT, 0);
    if (btn_slot_pm != NULL) lv_obj_set_style_bg_color(btn_slot_pm, !am ? CLR_ACCENT : lv_color_white(), 0);
    if (lbl_slot_pm != NULL) lv_obj_set_style_text_color(lbl_slot_pm, !am ? lv_color_white() : CLR_TEXT, 0);
    bool en = g_ready_en[g_sched_day_idx][g_sched_slot_idx];
    if (btn_slot_en != NULL) lv_obj_set_style_bg_color(btn_slot_en, en ? lv_palette_main(LV_PALETTE_GREEN) : lv_palette_main(LV_PALETTE_GREY), 0);
    if (lbl_slot_en != NULL) lv_label_set_text(lbl_slot_en, en ? LV_SYMBOL_OK "  On" : LV_SYMBOL_CLOSE "  Off");
}

static void update_time_labels() {
    char hb[4], mb[4];
    snprintf(hb, sizeof(hb), "%02d", g_ready_hh[g_sched_day_idx][g_sched_slot_idx]);
    snprintf(mb, sizeof(mb), "%02d", g_ready_mm[g_sched_day_idx][g_sched_slot_idx]);
    if (lbl_hh != NULL) lv_label_set_text(lbl_hh, hb);
    if (lbl_mm != NULL) lv_label_set_text(lbl_mm, mb);
    update_slot_buttons();
    recompute_next_preheat();
}

static void update_day_buttons() {
    bool wk = (g_sched_day_idx == 0);
    if (btn_day_wk != NULL) lv_obj_set_style_bg_color(btn_day_wk, wk ? CLR_ACCENT : lv_color_white(), 0);
    if (lbl_day_wk != NULL) lv_obj_set_style_text_color(lbl_day_wk, wk ? lv_color_white() : CLR_TEXT, 0);
    if (btn_day_we != NULL) lv_obj_set_style_bg_color(btn_day_we, !wk ? CLR_ACCENT : lv_color_white(), 0);
    if (lbl_day_we != NULL) lv_obj_set_style_text_color(lbl_day_we, !wk ? lv_color_white() : CLR_TEXT, 0);
}

// Three explicit operation modes, driven by one 3-way selector:
//   Manual   : g_auto_enabled = false                 (reactive — Home power button)
//   Ready-by : g_auto_enabled = true,  g_smart_learn = false
//   Smart    : g_auto_enabled = true,  g_smart_learn = true
static void update_mode_buttons() {
    bool manual = !g_auto_enabled;
    bool ready  =  g_auto_enabled && !g_smart_learn;
    bool smart  =  g_auto_enabled &&  g_smart_learn;

    if (btn_mode_manual != NULL) lv_obj_set_style_bg_color(btn_mode_manual, manual ? CLR_ACCENT : lv_color_white(), 0);
    if (lbl_mode_manual != NULL) lv_obj_set_style_text_color(lbl_mode_manual, manual ? lv_color_white() : CLR_TEXT, 0);
    if (btn_mode_ready  != NULL) lv_obj_set_style_bg_color(btn_mode_ready,  ready  ? CLR_ACCENT : lv_color_white(), 0);
    if (lbl_mode_ready  != NULL) lv_obj_set_style_text_color(lbl_mode_ready,  ready  ? lv_color_white() : CLR_TEXT, 0);
    if (btn_mode_smart  != NULL) lv_obj_set_style_bg_color(btn_mode_smart,  smart  ? CLR_ACCENT : lv_color_white(), 0);
    if (lbl_mode_smart  != NULL) lv_obj_set_style_text_color(lbl_mode_smart,  smart  ? lv_color_white() : CLR_TEXT, 0);

    if (panel_manual != NULL) { if (manual) lv_obj_clear_flag(panel_manual, LV_OBJ_FLAG_HIDDEN); else lv_obj_add_flag(panel_manual, LV_OBJ_FLAG_HIDDEN); }
    if (panel_ready  != NULL) { if (ready)  lv_obj_clear_flag(panel_ready,  LV_OBJ_FLAG_HIDDEN); else lv_obj_add_flag(panel_ready,  LV_OBJ_FLAG_HIDDEN); }
    if (panel_smart  != NULL) { if (smart)  lv_obj_clear_flag(panel_smart,  LV_OBJ_FLAG_HIDDEN); else lv_obj_add_flag(panel_smart,  LV_OBJ_FLAG_HIDDEN); }

    // Right column (next pre-heat + skip-today) is meaningless in Manual mode.
    if (sched_right_col != NULL) { if (manual) lv_obj_add_flag(sched_right_col, LV_OBJ_FLAG_HIDDEN); else lv_obj_clear_flag(sched_right_col, LV_OBJ_FLAG_HIDDEN); }
}

static void sched_mode_manual_cb(lv_event_t* e) { last_touch_time = millis(); g_auto_enabled = false;                        update_mode_buttons(); update_auto_badge(); }
static void sched_mode_ready_cb (lv_event_t* e) { last_touch_time = millis(); g_auto_enabled = true;  g_smart_learn = false; update_mode_buttons(); update_auto_badge(); }
static void sched_mode_smart_cb (lv_event_t* e) { last_touch_time = millis(); g_auto_enabled = true;  g_smart_learn = true;  update_mode_buttons(); update_auto_badge(); }
static void sched_day_wk_cb(lv_event_t* e) { last_touch_time = millis(); g_sched_day_idx = 0; update_day_buttons(); update_time_labels(); }
static void sched_day_we_cb(lv_event_t* e) { last_touch_time = millis(); g_sched_day_idx = 1; update_day_buttons(); update_time_labels(); }
static void sched_slot_am_cb(lv_event_t* e) { last_touch_time = millis(); g_sched_slot_idx = 0; update_time_labels(); }
static void sched_slot_pm_cb(lv_event_t* e) { last_touch_time = millis(); g_sched_slot_idx = 1; update_time_labels(); }
static void sched_slot_en_cb(lv_event_t* e) { last_touch_time = millis(); g_ready_en[g_sched_day_idx][g_sched_slot_idx] = !g_ready_en[g_sched_day_idx][g_sched_slot_idx]; update_slot_buttons(); recompute_next_preheat(); }
static void sched_hh_up_cb(lv_event_t* e) { last_touch_time = millis(); g_ready_hh[g_sched_day_idx][g_sched_slot_idx] = (g_ready_hh[g_sched_day_idx][g_sched_slot_idx] + 1) % 24; update_time_labels(); }
static void sched_hh_dn_cb(lv_event_t* e) { last_touch_time = millis(); g_ready_hh[g_sched_day_idx][g_sched_slot_idx] = (g_ready_hh[g_sched_day_idx][g_sched_slot_idx] + 23) % 24; update_time_labels(); }
static void sched_mm_up_cb(lv_event_t* e) { last_touch_time = millis(); g_ready_mm[g_sched_day_idx][g_sched_slot_idx] = (g_ready_mm[g_sched_day_idx][g_sched_slot_idx] + 5) % 60; update_time_labels(); }
static void sched_mm_dn_cb(lv_event_t* e) { last_touch_time = millis(); g_ready_mm[g_sched_day_idx][g_sched_slot_idx] = (g_ready_mm[g_sched_day_idx][g_sched_slot_idx] + 55) % 60; update_time_labels(); }

static void sched_skip_cb(lv_event_t* e) {
    last_touch_time = millis();
    g_skip_today = !g_skip_today;
    if (lbl_skip_btn != NULL)
        lv_label_set_text(lbl_skip_btn, g_skip_today ? LV_SYMBOL_OK "  Auto skipped today" : LV_SYMBOL_NEXT "  Skip auto today");
}

static void goto_schedule_cb(lv_event_t* e) { last_touch_time = millis(); show_page(page_schedule); }
static void goto_settings_cb(lv_event_t* e) { last_touch_time = millis(); show_page(page_settings); }
static void goto_stats_cb(lv_event_t* e)    { last_touch_time = millis(); show_page(page_stats); }
static void goto_solar_cb(lv_event_t* e)    { last_touch_time = millis(); show_page(page_solar); }
static void goto_diagnostics_cb(lv_event_t* e) { last_touch_time = millis(); show_page(page_diagnostics); }

// ---------------------------------------------------------------------------
//  Weather
// ---------------------------------------------------------------------------
void fetchWeather() {
    if (WiFi.status() != WL_CONNECTED) return;
    HTTPClient http;
    String url = "http://api.openweathermap.org/data/2.5/weather?q="
                 + String(WEATHER_CITY) + "," + String(WEATHER_COUNTRY_CODE)
                 + "&appid=" + String(WEATHER_API_KEY) + "&units=metric";
    http.begin(url);
    int code = http.GET();
    if (code == 200) {
        JsonDocument doc;
        if (!deserializeJson(doc, http.getString())) {
            float       temp      = doc["main"]["temp"];
            const char* condition = doc["weather"][0]["main"];
            UI_UpdateWeather(temp, condition);
            last_weather_update = millis();
        } else {
            Serial.println("Weather fetch: failed to parse JSON response");
        }
    } else {
        Serial.printf("Weather fetch failed, HTTP code: %d\n", code);
    }
    http.end();
}

// ---------------------------------------------------------------------------
//  Solar irradiance forecast (Open-Meteo, no API key required)
//  forecast_days=1 -> exactly 24 hourly entries, so array index == hour.
// ---------------------------------------------------------------------------
#define SOLAR_HOURS 24
#define SOLAR_FORECAST_URL \
    "https://api.open-meteo.com/v1/forecast?latitude=32.08&longitude=34.78" \
    "&hourly=shortwave_radiation,direct_radiation,diffuse_radiation" \
    "&timezone=Asia%2FJerusalem&forecast_days=1"

static float g_solar_ghi[SOLAR_HOURS]     = {0};   // shortwave_radiation (W/m^2) - main panel-output signal
static float g_solar_direct[SOLAR_HOURS]  = {0};
static float g_solar_diffuse[SOLAR_HOURS] = {0};
static bool  g_solar_loaded = false;

// Peak irradiance, in plain words, for someone who doesn't know whether
// "910 W/m2" is a lot: clear-sky solar noon tops out around 1000 W/m2.
static const char* solarLevelLabel(float w) {
    if (w >= 650.0f) return "High";
    if (w >= 300.0f) return "Moderate";
    return "Low";
}

static lv_color_t solarLevelColor(float w) {
    if (w >= 650.0f) return lv_palette_main(LV_PALETTE_GREEN);
    if (w >= 300.0f) return lv_palette_main(LV_PALETTE_ORANGE);
    return CLR_SUBTEXT;
}

// Pushes the in-memory forecast into the Solar page chart, if built.
static void refreshSolarChart() {
    if (chart_solar == NULL || ser_solar == NULL) return;

    float peak_val = 0.0f;
    int   peak_hr  = 0;
    for (int i = 0; i < SOLAR_HOURS; i++) {
        lv_chart_set_value_by_id(chart_solar, ser_solar, i, (lv_coord_t)(g_solar_ghi[i] + 0.5f));
        if (g_solar_ghi[i] > peak_val) { peak_val = g_solar_ghi[i]; peak_hr = i; }
    }
    lv_chart_refresh(chart_solar);

    if (lbl_solar_peak != NULL) {
        char buf[48];
        if (g_solar_loaded) {
            snprintf(buf, sizeof(buf), "Peak: %.0f W/m2 at %02d:00 (%s)",
                     peak_val, peak_hr, solarLevelLabel(peak_val));
            lv_obj_set_style_text_color(lbl_solar_peak, solarLevelColor(peak_val), 0);
        } else {
            snprintf(buf, sizeof(buf), "Peak: -- W/m2");
            lv_obj_set_style_text_color(lbl_solar_peak, CLR_SUBTEXT, 0);
        }
        lv_label_set_text(lbl_solar_peak, buf);
    }
}

// Formats major X-axis ticks as "HH:00" for our 24-hour charts. Pairs with
// lv_chart_set_axis_tick(..., major_cnt=5, minor_cnt=1, ...) so tick
// ordinal 0..4 maps to hour 0, 6, 12, 18, 24.
static void hourly_chart_x_tick_cb(lv_event_t* e) {
    lv_obj_draw_part_dsc_t* dsc = lv_event_get_draw_part_dsc(e);
    if (dsc->type != LV_CHART_DRAW_PART_TICK_LABEL) return;
    if (dsc->id != LV_CHART_AXIS_PRIMARY_X || dsc->text == NULL) return;
    lv_snprintf(dsc->text, dsc->text_length, "%02d:00", (int)dsc->value * 6);
}

void fetchSolarForecast() {
    if (WiFi.status() != WL_CONNECTED) return;
    HTTPClient http;
    http.begin(SOLAR_FORECAST_URL);
    int code = http.GET();
    if (code == 200) {
        JsonDocument doc;
        if (!deserializeJson(doc, http.getString())) {
            JsonArray ghi     = doc["hourly"]["shortwave_radiation"];
            JsonArray direct  = doc["hourly"]["direct_radiation"];
            JsonArray diffuse = doc["hourly"]["diffuse_radiation"];
            for (int i = 0; i < SOLAR_HOURS && i < (int)ghi.size();     i++) g_solar_ghi[i]     = ghi[i];
            for (int i = 0; i < SOLAR_HOURS && i < (int)direct.size();  i++) g_solar_direct[i]  = direct[i];
            for (int i = 0; i < SOLAR_HOURS && i < (int)diffuse.size(); i++) g_solar_diffuse[i] = diffuse[i];
            g_solar_loaded = true;
            if (lvgl_port_lock(UI_REFRESH_RATE)) {
                refreshSolarChart();
                lvgl_port_unlock();
            }
        } else {
            Serial.println("Solar forecast: failed to parse JSON response");
        }
    } else {
        Serial.printf("Solar forecast fetch failed, HTTP code: %d\n", code);
    }
    http.end();
}

// ---------------------------------------------------------------------------
//  Water usage tracking (Stats page)
//  Blue (cool) -> red (hot) color scale used to encode each hour's tank
//  temperature on the usage chart's bars.
// ---------------------------------------------------------------------------
static lv_color_t usageTempToColor(float t) {
    float f = (t - 20.0f) / 50.0f;   // 20-70 degC mapped to 0-1
    if (f < 0.0f) f = 0.0f;
    if (f > 1.0f) f = 1.0f;
    uint8_t r = (uint8_t)(0x64 + f * (0xD3 - 0x64));
    uint8_t g = (uint8_t)(0xB5 + f * (0x2F - 0xB5));
    uint8_t b = (uint8_t)(0xF6 + f * (0x2F - 0xF6));
    return lv_color_make(r, g, b);
}

static void usage_chart_draw_event_cb(lv_event_t* e) {
    lv_obj_draw_part_dsc_t* dsc = lv_event_get_draw_part_dsc(e);
    if (dsc->part != LV_PART_ITEMS || dsc->type != LV_CHART_DRAW_PART_BAR) return;
    if (dsc->id < 0 || dsc->id >= USAGE_HOURS) return;
    dsc->rect_dsc->bg_color = usageTempToColor(g_hourly_temp[dsc->id]);
}

// Pushes the in-memory hourly buckets into the Stats page chart, if built.
static void refreshUsageChart() {
    if (chart_usage == NULL || ser_usage == NULL) return;
    float total = 0.0f;
    for (int i = 0; i < USAGE_HOURS; i++) {
        lv_chart_set_value_by_id(chart_usage, ser_usage, i, (lv_coord_t)(g_hourly_liters[i] + 0.5f));
        total += g_hourly_liters[i];
    }
    lv_chart_refresh(chart_usage);
    if (lbl_usage_today != NULL) {
        char buf[32];
        snprintf(buf, sizeof(buf), "Today: %.0f L", total);
        lv_label_set_text(lbl_usage_today, buf);
    }
}

// Called once per second from UI_UpdateSensorData with the live flow/temp
// readings. Integrates flow over elapsed time into the current hour's
// bucket, rolls over at midnight, and persists to flash periodically.
static void updateWaterUsage(float t_internal, float flow) {
    struct tm timeinfo;
    if (!getLocalTime(&timeinfo, 5)) return;   // no synced clock yet

    int day  = timeinfo.tm_yday;
    int hour = timeinfo.tm_hour;

    if (g_usage_day == -1) {
        // First call after boot: resume today's saved progress, if any.
        int   saved_day = -1;
        float liters[USAGE_HOURS], temps[USAGE_HOURS];
        if (DataManager::loadWaterUsage(saved_day, liters, temps, USAGE_HOURS) && saved_day == day) {
            memcpy(g_hourly_liters, liters, sizeof(g_hourly_liters));
            memcpy(g_hourly_temp,   temps,  sizeof(g_hourly_temp));
        }
        g_usage_day     = day;
        g_last_usage_ms = millis();
        return;
    }

    if (day != g_usage_day) {
        // Midnight rollover: start today fresh.
        memset(g_hourly_liters, 0, sizeof(g_hourly_liters));
        memset(g_hourly_temp,   0, sizeof(g_hourly_temp));
        g_usage_day = day;
    }

    unsigned long now = millis();
    float dt_min = (now - g_last_usage_ms) / 60000.0f;
    g_last_usage_ms = now;
    if (dt_min > 0.0f && dt_min < 5.0f) {   // ignore absurd gaps (reboot, clock jump)
        g_hourly_liters[hour] += flow * dt_min;
    }
    g_hourly_temp[hour] = t_internal;

    if (now - g_last_usage_save_ms > 300000UL) {   // persist every 5 minutes
        g_last_usage_save_ms = now;
        DataManager::saveWaterUsage(g_usage_day, g_hourly_liters, g_hourly_temp, USAGE_HOURS);
    }
}

// ---------------------------------------------------------------------------
//  Screensaver
// ---------------------------------------------------------------------------
static void createScreensaver(lv_obj_t* parent) {
    screensaver = lv_obj_create(parent);
    disableScroll(screensaver);
    lv_obj_set_size(screensaver, 800, 480);
    lv_obj_set_pos(screensaver, 0, 0);
    lv_obj_set_style_bg_color(screensaver, lv_color_hex(0x0A0A1A), 0);
    lv_obj_set_style_bg_opa(screensaver, LV_OPA_COVER, 0);
    lv_obj_set_style_border_width(screensaver, 0, 0);
    lv_obj_add_event_cb(screensaver, screen_touched_cb, LV_EVENT_CLICKED, NULL);

    lv_obj_t* title = lv_label_create(screensaver);
    lv_label_set_text(title, "SMART BOILER");
    lv_obj_set_style_text_font(title, &lv_font_montserrat_48, 0);
    lv_obj_set_style_text_color(title, lv_color_white(), 0);
    lv_obj_align(title, LV_ALIGN_CENTER, 0, -80);

    screensaver_time = lv_label_create(screensaver);
    lv_label_set_text(screensaver_time, "--:--");
    lv_obj_set_style_text_font(screensaver_time, &lv_font_montserrat_48, 0);
    lv_obj_set_style_text_color(screensaver_time, lv_color_hex(0x90CAF9), 0);
    lv_obj_align(screensaver_time, LV_ALIGN_CENTER, 0, 20);

    screensaver_date = lv_label_create(screensaver);
    lv_label_set_text(screensaver_date, "");
    lv_obj_set_style_text_font(screensaver_date, &lv_font_montserrat_24, 0);
    lv_obj_set_style_text_color(screensaver_date, lv_color_hex(0xAAAAAA), 0);
    lv_obj_align(screensaver_date, LV_ALIGN_CENTER, 0, 80);

    lv_obj_t* hint = lv_label_create(screensaver);
    lv_label_set_text(hint, "Tap to wake");
    lv_obj_set_style_text_font(hint, &lv_font_montserrat_14, 0);
    lv_obj_set_style_text_color(hint, lv_color_hex(0x555566), 0);
    lv_obj_align(hint, LV_ALIGN_BOTTOM_MID, 0, -30);

    lv_obj_add_flag(screensaver, LV_OBJ_FLAG_HIDDEN);
}

void checkScreensaver() {
    if (screensaver == NULL) return;
    if (millis() - last_touch_time > SCREENSAVER_TIMEOUT &&
        !lv_obj_is_visible(screensaver))
        lv_obj_clear_flag(screensaver, LV_OBJ_FLAG_HIDDEN);
}

// ---------------------------------------------------------------------------
//  Diagnostics live-refresh timer (heap / uptime / RSSI — not packet-driven)
// ---------------------------------------------------------------------------
static void diag_timer_cb(lv_timer_t* t) {
    (void)t;
    if (lbl_diag_heap != NULL) {
        char buf[24];
        snprintf(buf, sizeof(buf), "%u kB", (unsigned)(ESP.getFreeHeap() / 1024));
        lv_label_set_text(lbl_diag_heap, buf);
    }
    if (lbl_diag_uptime != NULL) {
        unsigned long s = millis() / 1000;
        char buf[16];
        snprintf(buf, sizeof(buf), "%02lu:%02lu:%02lu", s / 3600, (s / 60) % 60, s % 60);
        lv_label_set_text(lbl_diag_uptime, buf);
    }
    if (lbl_diag_rssi != NULL) {
        char buf[16];
        if (WiFi.status() == WL_CONNECTED) snprintf(buf, sizeof(buf), "%d dBm", WiFi.RSSI());
        else                               snprintf(buf, sizeof(buf), "--");
        lv_label_set_text(lbl_diag_rssi, buf);
    }
}

// ===========================================================================
//  Page builders
// ===========================================================================
static void build_home_page(lv_obj_t* scr) {
    page_home = lv_obj_create(scr);
    disableScroll(page_home);
    lv_obj_set_size(page_home, 800, 480);
    lv_obj_set_pos(page_home, 0, 0);
    lv_obj_set_style_bg_color(page_home, CLR_BG, 0);
    lv_obj_set_style_border_width(page_home, 0, 0);
    lv_obj_set_style_radius(page_home, 0, 0);
    lv_obj_set_style_pad_all(page_home, 0, 0);

    // --- Top bar (800 x 55) ---
    lv_obj_t* top_bar = lv_obj_create(page_home);
    disableScroll(top_bar);
    lv_obj_set_size(top_bar, 800, 55);
    lv_obj_set_pos(top_bar, 0, 0);
    lv_obj_set_style_bg_color(top_bar, CLR_TOPBAR, 0);
    lv_obj_set_style_border_width(top_bar, 0, 0);
    lv_obj_set_style_radius(top_bar, 0, 0);
    lv_obj_set_style_pad_hor(top_bar, 14, 0);
    lv_obj_set_style_pad_ver(top_bar, 0, 0);
    lv_obj_set_style_pad_column(top_bar, 10, 0);
    lv_obj_set_flex_flow(top_bar, LV_FLEX_FLOW_ROW);
    lv_obj_set_flex_align(top_bar, LV_FLEX_ALIGN_START, LV_FLEX_ALIGN_CENTER, LV_FLEX_ALIGN_CENTER);

    lv_obj_t* wifi_btn = lv_btn_create(top_bar);
    lv_obj_set_size(wifi_btn, 50, 42);
    lv_obj_set_style_radius(wifi_btn, 10, 0);
    lv_obj_set_style_bg_opa(wifi_btn, LV_OPA_20, 0);
    lv_obj_set_style_border_width(wifi_btn, 0, 0);
    lv_obj_add_event_cb(wifi_btn, wifi_icon_click_event_cb, LV_EVENT_CLICKED, NULL);
    lbl_wifi_icon = lv_label_create(wifi_btn);
    lv_label_set_text(lbl_wifi_icon, LV_SYMBOL_WIFI);
    lv_obj_set_style_text_font(lbl_wifi_icon, &lv_font_montserrat_22, 0);
    lv_obj_set_style_text_color(lbl_wifi_icon, lv_palette_main(LV_PALETTE_RED), 0);
    lv_obj_center(lbl_wifi_icon);

    btn_auto_badge = lv_btn_create(top_bar);
    lv_obj_set_width(btn_auto_badge, LV_SIZE_CONTENT);
    lv_obj_set_height(btn_auto_badge, 42);
    lv_obj_set_style_radius(btn_auto_badge, 21, 0);
    lv_obj_set_style_bg_color(btn_auto_badge, lv_palette_main(LV_PALETTE_GREEN), 0);
    lv_obj_set_style_border_width(btn_auto_badge, 0, 0);
    lv_obj_set_style_pad_hor(btn_auto_badge, 14, 0);
    lv_obj_add_event_cb(btn_auto_badge, goto_schedule_cb, LV_EVENT_CLICKED, NULL);
    lbl_auto_badge = lv_label_create(btn_auto_badge);
    lv_label_set_text(lbl_auto_badge, LV_SYMBOL_CHARGE "  Auto");
    lv_obj_set_style_text_font(lbl_auto_badge, &lv_font_montserrat_16, 0);
    lv_obj_set_style_text_color(lbl_auto_badge, lv_color_white(), 0);
    lv_obj_center(lbl_auto_badge);

    lv_obj_t* center_box = lv_obj_create(top_bar);
    disableScroll(center_box);
    lv_obj_set_flex_grow(center_box, 1);
    lv_obj_set_height(center_box, 48);
    lv_obj_set_style_bg_opa(center_box, LV_OPA_TRANSP, 0);
    lv_obj_set_style_border_width(center_box, 0, 0);
    lv_obj_set_style_pad_all(center_box, 0, 0);
    lv_obj_set_flex_flow(center_box, LV_FLEX_FLOW_ROW);
    lv_obj_set_flex_align(center_box, LV_FLEX_ALIGN_CENTER, LV_FLEX_ALIGN_CENTER, LV_FLEX_ALIGN_CENTER);
    lv_obj_set_style_pad_column(center_box, 12, 0);

    lbl_time = lv_label_create(center_box);
    lv_label_set_text(lbl_time, "--:--");
    lv_obj_set_style_text_font(lbl_time, &lv_font_montserrat_28, 0);
    lv_obj_set_style_text_color(lbl_time, lv_color_white(), 0);

    lbl_date = lv_label_create(center_box);
    lv_label_set_text(lbl_date, "");
    lv_obj_set_style_text_font(lbl_date, &lv_font_montserrat_14, 0);
    lv_obj_set_style_text_color(lbl_date, lv_color_hex(0xBBCCEE), 0);

    lv_obj_t* weather_row = lv_obj_create(top_bar);
    disableScroll(weather_row);
    lv_obj_set_size(weather_row, 90, 48);
    lv_obj_set_style_bg_opa(weather_row, LV_OPA_TRANSP, 0);
    lv_obj_set_style_border_width(weather_row, 0, 0);
    lv_obj_set_style_pad_all(weather_row, 0, 0);
    lv_obj_set_flex_flow(weather_row, LV_FLEX_FLOW_ROW);
    lv_obj_set_flex_align(weather_row, LV_FLEX_ALIGN_END, LV_FLEX_ALIGN_CENTER, LV_FLEX_ALIGN_CENTER);
    lv_obj_set_style_pad_column(weather_row, 6, 0);

    lbl_weather_icon = lv_label_create(weather_row);
    lv_label_set_text(lbl_weather_icon, LV_SYMBOL_IMAGE);
    lv_obj_set_style_text_font(lbl_weather_icon, &lv_font_montserrat_20, 0);
    lv_obj_set_style_text_color(lbl_weather_icon, lv_color_hex(0xFFD54F), 0);

    lbl_weather_temp = lv_label_create(weather_row);
    lv_label_set_text(lbl_weather_temp, "--\xc2\xb0");
    lv_obj_set_style_text_font(lbl_weather_temp, &lv_font_montserrat_20, 0);
    lv_obj_set_style_text_color(lbl_weather_temp, lv_color_white(), 0);

    // --- Middle row (800 x 270, y=55) ---
    lv_obj_t* mid_row = lv_obj_create(page_home);
    disableScroll(mid_row);
    lv_obj_set_size(mid_row, 800, 270);
    lv_obj_set_pos(mid_row, 0, 55);
    lv_obj_set_style_bg_opa(mid_row, LV_OPA_TRANSP, 0);
    lv_obj_set_style_border_width(mid_row, 0, 0);
    lv_obj_set_style_pad_hor(mid_row, 18, 0);
    lv_obj_set_style_pad_ver(mid_row, 16, 0);
    lv_obj_set_flex_flow(mid_row, LV_FLEX_FLOW_ROW);
    lv_obj_set_flex_align(mid_row, LV_FLEX_ALIGN_START, LV_FLEX_ALIGN_CENTER, LV_FLEX_ALIGN_CENTER);
    lv_obj_set_style_pad_column(mid_row, 18, 0);

    lv_obj_t* circle_col = lv_obj_create(mid_row);
    disableScroll(circle_col);
    lv_obj_set_size(circle_col, 340, 230);
    lv_obj_set_style_bg_opa(circle_col, LV_OPA_TRANSP, 0);
    lv_obj_set_style_border_width(circle_col, 0, 0);
    lv_obj_set_style_pad_all(circle_col, 0, 0);
    lv_obj_set_flex_flow(circle_col, LV_FLEX_FLOW_ROW);
    lv_obj_set_flex_align(circle_col, LV_FLEX_ALIGN_CENTER, LV_FLEX_ALIGN_CENTER, LV_FLEX_ALIGN_CENTER);

    temp_circle_obj = lv_obj_create(circle_col);
    disableScroll(temp_circle_obj);
    lv_obj_set_size(temp_circle_obj, 218, 218);
    lv_obj_set_style_radius(temp_circle_obj, LV_RADIUS_CIRCLE, 0);
    lv_obj_set_style_bg_color(temp_circle_obj, lv_color_white(), 0);
    lv_obj_set_style_border_width(temp_circle_obj, 8, 0);
    lv_obj_set_style_border_color(temp_circle_obj, CLR_ACCENT, 0);
    lv_obj_set_style_shadow_width(temp_circle_obj, 24, 0);
    lv_obj_set_style_shadow_opa(temp_circle_obj, LV_OPA_20, 0);
    lv_obj_set_flex_flow(temp_circle_obj, LV_FLEX_FLOW_COLUMN);
    lv_obj_set_flex_align(temp_circle_obj, LV_FLEX_ALIGN_CENTER, LV_FLEX_ALIGN_CENTER, LV_FLEX_ALIGN_CENTER);
    lv_obj_set_style_pad_row(temp_circle_obj, 4, 0);

    lv_obj_t* lbl_water_title = lv_label_create(temp_circle_obj);
    lv_label_set_text(lbl_water_title, "Water Temp");
    lv_obj_set_style_text_font(lbl_water_title, &lv_font_montserrat_14, 0);
    lv_obj_set_style_text_color(lbl_water_title, CLR_SUBTEXT, 0);

    lbl_water_temp = lv_label_create(temp_circle_obj);
    lv_label_set_text(lbl_water_temp, "--\xc2\xb0");
    lv_obj_set_style_text_font(lbl_water_temp, &lv_font_montserrat_48, 0);
    lv_obj_set_style_text_color(lbl_water_temp, CLR_ACCENT, 0);

    lbl_target_inline = lv_label_create(temp_circle_obj);
    lv_label_set_text(lbl_target_inline, "Target 60\xc2\xb0");
    lv_obj_set_style_text_font(lbl_target_inline, &lv_font_montserrat_14, 0);
    lv_obj_set_style_text_color(lbl_target_inline, CLR_SUBTEXT, 0);

    led_heating = lv_led_create(temp_circle_obj);
    lv_obj_set_size(led_heating, 1, 1);   // kept for API compatibility, not shown
    lv_obj_add_flag(led_heating, LV_OBJ_FLAG_HIDDEN);

    lv_obj_t* right_col = lv_obj_create(mid_row);
    disableScroll(right_col);
    lv_obj_set_flex_grow(right_col, 1);
    lv_obj_set_height(right_col, 236);
    lv_obj_set_style_bg_opa(right_col, LV_OPA_TRANSP, 0);
    lv_obj_set_style_border_width(right_col, 0, 0);
    lv_obj_set_style_pad_all(right_col, 0, 0);
    lv_obj_set_flex_flow(right_col, LV_FLEX_FLOW_COLUMN);
    lv_obj_set_flex_align(right_col, LV_FLEX_ALIGN_CENTER, LV_FLEX_ALIGN_CENTER, LV_FLEX_ALIGN_CENTER);
    lv_obj_set_style_pad_row(right_col, 8, 0);

    btn_power = lv_btn_create(right_col);
    disableScroll(btn_power);
    lv_obj_set_size(btn_power, lv_pct(100), 150);
    lv_obj_set_style_radius(btn_power, 28, 0);
    lv_obj_set_style_bg_color(btn_power, CLR_OFF, 0);
    lv_obj_set_style_shadow_width(btn_power, 24, 0);
    lv_obj_set_style_shadow_opa(btn_power, LV_OPA_30, 0);
    lv_obj_add_event_cb(btn_power, power_btn_event_cb, LV_EVENT_CLICKED, NULL);

    lbl_power_status = lv_label_create(btn_power);
    lv_obj_set_style_text_font(lbl_power_status, &lv_font_montserrat_46, 0);
    lv_obj_set_style_text_color(lbl_power_status, lv_color_white(), 0);
    lv_obj_center(lbl_power_status);
    if (appMode == MODE_DEMO) {
        lv_label_set_text(lbl_power_status, "ON");
        lv_obj_set_style_bg_color(btn_power, CLR_ON, 0);
    } else {
        lv_label_set_text(lbl_power_status, "OFF");
    }

    lv_obj_t* shower_card = lv_obj_create(right_col);
    disableScroll(shower_card);
    lv_obj_set_size(shower_card, lv_pct(100), 78);
    lv_obj_set_style_radius(shower_card, 20, 0);
    lv_obj_set_style_bg_color(shower_card, lv_color_white(), 0);
    lv_obj_set_style_border_width(shower_card, 2, 0);
    lv_obj_set_style_border_color(shower_card, CLR_BORDER, 0);
    lv_obj_set_flex_flow(shower_card, LV_FLEX_FLOW_ROW);
    lv_obj_set_flex_align(shower_card, LV_FLEX_ALIGN_CENTER, LV_FLEX_ALIGN_CENTER, LV_FLEX_ALIGN_CENTER);
    lv_obj_set_style_pad_column(shower_card, 10, 0);

    lv_obj_t* droplet = lv_label_create(shower_card);
    lv_label_set_text(droplet, LV_SYMBOL_TINT);
    lv_obj_set_style_text_font(droplet, &lv_font_montserrat_24, 0);
    lv_obj_set_style_text_color(droplet, CLR_SUBTEXT, 0);

    lbl_shower_readiness = lv_label_create(shower_card);
    lv_label_set_text(lbl_shower_readiness, "Connecting...");
    lv_obj_set_style_text_font(lbl_shower_readiness, &lv_font_montserrat_20, 0);
    lv_obj_set_style_text_color(lbl_shower_readiness, CLR_SUBTEXT, 0);

    // --- Tile row (800 x 155, y=325) ---
    lv_obj_t* tile_row = lv_obj_create(page_home);
    disableScroll(tile_row);
    lv_obj_set_size(tile_row, 800, 155);
    lv_obj_set_pos(tile_row, 0, 325);
    lv_obj_set_style_bg_opa(tile_row, LV_OPA_TRANSP, 0);
    lv_obj_set_style_border_width(tile_row, 0, 0);
    lv_obj_set_style_pad_hor(tile_row, 18, 0);
    lv_obj_set_style_pad_ver(tile_row, 0, 0);
    lv_obj_set_flex_flow(tile_row, LV_FLEX_FLOW_ROW);
    lv_obj_set_flex_align(tile_row, LV_FLEX_ALIGN_SPACE_EVENLY, LV_FLEX_ALIGN_CENTER, LV_FLEX_ALIGN_CENTER);
    lv_obj_set_style_pad_column(tile_row, 18, 0);

    make_tile(tile_row, LV_SYMBOL_SETTINGS, "Settings",
              lv_color_hex(0xE3F2FD), lv_color_hex(0xBBDEFB), lv_color_hex(0x0C447C), goto_settings_cb);
    make_tile(tile_row, LV_SYMBOL_WIFI, "Network",
              lv_color_hex(0xE8F5E9), lv_color_hex(0xC8E6C9), lv_color_hex(0x1B5E20), goto_network_cb);
    make_tile(tile_row, LV_SYMBOL_BARS, "Stats",
              lv_color_hex(0xFFF3E0), lv_color_hex(0xFFE0B2), lv_color_hex(0xBF360C), goto_stats_cb);
    make_tile(tile_row, LV_SYMBOL_IMAGE, "Solar",
              lv_color_hex(0xFFF8E1), lv_color_hex(0xFFECB3), lv_color_hex(0xF57F17), goto_solar_cb);

    lv_obj_add_event_cb(page_home, screen_touched_cb, LV_EVENT_PRESSED, NULL);
}

static void apply_mode_switch() {
    appMode = (appMode == MODE_DEMO) ? MODE_REALTIME : MODE_DEMO;
    demo_stop_comms   = false;
    demo_fault_sim    = false;
    demo_solar_active = false;
    demo_ui_on        = true;
    demo_temp         = 35.0f;
    demo_flow         = 0.0f;
    if (lbl_app_mode != NULL) {
        lv_label_set_text(lbl_app_mode,
                          appMode == MODE_DEMO ? LV_SYMBOL_PLAY "  Data: Demo"
                                               : LV_SYMBOL_EYE_OPEN "  Data: Real-time");
    }
    if (btn_app_mode != NULL) {
        lv_obj_set_style_bg_color(btn_app_mode, appMode == MODE_DEMO ? CLR_WAITING : CLR_ON, 0);
    }
    if (appMode == MODE_DEMO) {
        if (btn_power        != NULL) lv_obj_set_style_bg_color(btn_power, CLR_ON, 0);
        if (lbl_power_status != NULL) lv_label_set_text(lbl_power_status, "ON");
    } else {
        if (btn_power        != NULL) lv_obj_set_style_bg_color(btn_power, boiler_state ? CLR_ON : CLR_OFF, 0);
        if (lbl_power_status != NULL) lv_label_set_text(lbl_power_status, boiler_state ? "ON" : "OFF");
    }
    DataManager::saveAppMode((uint8_t)appMode);
    Serial.printf("[UI] Mode switched to: %s (persisted)\n",
                  appMode == MODE_DEMO ? "DEMO" : "REALTIME");
}

static void mode_confirm_cb(lv_event_t* e) {
    lv_obj_t* mbox = lv_event_get_current_target(e);
    const char* btn_txt = lv_msgbox_get_active_btn_text(mbox);
    if (btn_txt == NULL) return;
    if (strcmp(btn_txt, "Yes") == 0) {
        apply_mode_switch();
    }
    lv_msgbox_close(mbox);
}

static void mode_toggle_cb(lv_event_t*) {
    last_touch_time = millis();
    const char* target = (appMode == MODE_DEMO) ? "Real-time" : "Demo";
    char msg[64];
    snprintf(msg, sizeof(msg), "Switch to %s mode?", target);
    static const char* btns[] = {"Yes", "Cancel", ""};
    lv_obj_t* mbox = lv_msgbox_create(NULL, "Confirm", msg, btns, false);
    lv_obj_set_style_text_font(mbox, &lv_font_montserrat_20, 0);
    lv_obj_center(mbox);
    lv_obj_add_event_cb(mbox, mode_confirm_cb, LV_EVENT_VALUE_CHANGED, NULL);
}

// ---------------------------------------------------------------------------
//  Setup Wizard — 3-step onboarding, entered from Settings
// ---------------------------------------------------------------------------
static void update_wizard_temp_label() {
    if (lbl_wiz_temp == NULL) return;
    char buf[8];
    snprintf(buf, sizeof(buf), "%d\xc2\xb0", wiz_temp);
    lv_label_set_text(lbl_wiz_temp, buf);
}
static void wiz_temp_up_cb(lv_event_t*) { last_touch_time = millis(); if (wiz_temp < 65) { wiz_temp += 5; update_wizard_temp_label(); } }
static void wiz_temp_dn_cb(lv_event_t*) { last_touch_time = millis(); if (wiz_temp > 25) { wiz_temp -= 5; update_wizard_temp_label(); } }

static void update_wizard_household_label() {
    if (lbl_wiz_household == NULL) return;
    char buf[8];
    snprintf(buf, sizeof(buf), "%d", wiz_household);
    lv_label_set_text(lbl_wiz_household, buf);
}
static void wiz_household_up_cb(lv_event_t*) { last_touch_time = millis(); if (wiz_household < 8) { wiz_household++; update_wizard_household_label(); } }
static void wiz_household_dn_cb(lv_event_t*) { last_touch_time = millis(); if (wiz_household > 1) { wiz_household--; update_wizard_household_label(); } }

static void update_wizard_time_labels() {
    char hb[4], mb[4];
    snprintf(hb, sizeof(hb), "%02d", wiz_ready_hh);
    snprintf(mb, sizeof(mb), "%02d", wiz_ready_mm);
    if (lbl_wiz_hh != NULL) lv_label_set_text(lbl_wiz_hh, hb);
    if (lbl_wiz_mm != NULL) lv_label_set_text(lbl_wiz_mm, mb);
}
static void wiz_hh_up_cb(lv_event_t*) { last_touch_time = millis(); wiz_ready_hh = (wiz_ready_hh + 1) % 24; update_wizard_time_labels(); }
static void wiz_hh_dn_cb(lv_event_t*) { last_touch_time = millis(); wiz_ready_hh = (wiz_ready_hh + 23) % 24; update_wizard_time_labels(); }
static void wiz_mm_up_cb(lv_event_t*) { last_touch_time = millis(); wiz_ready_mm = (wiz_ready_mm + 5) % 60; update_wizard_time_labels(); }
static void wiz_mm_dn_cb(lv_event_t*) { last_touch_time = millis(); wiz_ready_mm = (wiz_ready_mm + 55) % 60; update_wizard_time_labels(); }

static void update_wizard_step_ui() {
    if (wiz_step_temp == NULL) return;
    lv_obj_t* steps[] = { wiz_step_temp, wiz_step_household, wiz_step_schedule };
    for (lv_obj_t* s : steps) lv_obj_add_flag(s, LV_OBJ_FLAG_HIDDEN);
    lv_obj_clear_flag(steps[wizard_step], LV_OBJ_FLAG_HIDDEN);

    if (lbl_wiz_progress != NULL) {
        char buf[16];
        snprintf(buf, sizeof(buf), "Step %d of 3", wizard_step + 1);
        lv_label_set_text(lbl_wiz_progress, buf);
    }
    if (btn_wiz_back != NULL) {
        if (wizard_step == 0) lv_obj_add_flag(btn_wiz_back, LV_OBJ_FLAG_HIDDEN);
        else                  lv_obj_clear_flag(btn_wiz_back, LV_OBJ_FLAG_HIDDEN);
    }
    if (lbl_wiz_next_text != NULL) lv_label_set_text(lbl_wiz_next_text, wizard_step == 2 ? "Finish" : "Next");
}

static void wizard_finish_cb(lv_event_t*) {
    last_touch_time = millis();
    target_temperature = wiz_temp;
    updateTargetLabels();
    g_pref_household = wiz_household;
    g_pref_ready_hh   = wiz_ready_hh;
    g_pref_ready_mm   = wiz_ready_mm;
    // Apply the wizard's default time to the Schedule screen immediately (both
    // weekday & weekend), so it appears there and the brain uses it right away.
    g_ready_hh[0][0] = g_ready_hh[1][0] = wiz_ready_hh;   // wizard sets the Morning slot
    g_ready_mm[0][0] = g_ready_mm[1][0] = wiz_ready_mm;
    update_time_labels();
    DataManager::saveSetting("target_temp",    wiz_temp);
    DataManager::saveSetting("household_size", wiz_household);
    DataManager::saveSetting("ready_hh",       wiz_ready_hh);
    DataManager::saveSetting("ready_mm",       wiz_ready_mm);
    wizard_step = 0;
    update_wizard_step_ui();
    show_page(page_home);
}

static void wizard_next_cb(lv_event_t* e) {
    last_touch_time = millis();
    if (wizard_step < 2) {
        wizard_step++;
        update_wizard_step_ui();
    } else {
        wizard_finish_cb(e);
    }
}

static void wizard_back_cb(lv_event_t*) {
    last_touch_time = millis();
    if (wizard_step > 0) {
        wizard_step--;
        update_wizard_step_ui();
    }
}

static void goto_wizard_cb(lv_event_t*) {
    last_touch_time = millis();
    wiz_temp      = target_temperature;
    wiz_household = g_pref_household;
    wiz_ready_hh  = g_pref_ready_hh;
    wiz_ready_mm  = g_pref_ready_mm;
    wizard_step   = 0;
    update_wizard_temp_label();
    update_wizard_household_label();
    update_wizard_time_labels();
    update_wizard_step_ui();
    show_page(page_wizard);
}

static void build_settings_page(lv_obj_t* scr) {
    page_settings = lv_obj_create(scr);
    disableScroll(page_settings);
    lv_obj_set_size(page_settings, 800, 480);
    lv_obj_set_pos(page_settings, 0, 0);
    lv_obj_set_style_bg_color(page_settings, CLR_BG, 0);
    lv_obj_set_style_border_width(page_settings, 0, 0);
    lv_obj_set_style_radius(page_settings, 0, 0);
    lv_obj_set_style_pad_all(page_settings, 0, 0);
    lv_obj_add_flag(page_settings, LV_OBJ_FLAG_HIDDEN);

    lv_obj_t* header = make_header(page_settings, CLR_TOPBAR);
    make_back_btn(header, page_home);
    make_header_title(header, "Settings");

    lv_obj_t* body = lv_obj_create(page_settings);
    disableScroll(body);
    lv_obj_set_size(body, 800, 416);
    lv_obj_set_pos(body, 0, 64);
    lv_obj_set_style_bg_opa(body, LV_OPA_TRANSP, 0);
    lv_obj_set_style_border_width(body, 0, 0);
    lv_obj_set_style_pad_all(body, 22, 0);

    lv_obj_t* lbl_target_title = lv_label_create(body);
    lv_label_set_text(lbl_target_title, "Target temperature");
    lv_obj_set_style_text_font(lbl_target_title, &lv_font_montserrat_16, 0);
    lv_obj_set_style_text_color(lbl_target_title, CLR_SUBTEXT, 0);
    lv_obj_align(lbl_target_title, LV_ALIGN_TOP_LEFT, 0, 0);

    lv_obj_t* ctrl_row = lv_obj_create(body);
    disableScroll(ctrl_row);
    lv_obj_set_size(ctrl_row, lv_pct(100), 130);
    lv_obj_set_pos(ctrl_row, 0, 36);
    lv_obj_set_style_bg_color(ctrl_row, lv_color_white(), 0);
    lv_obj_set_style_border_width(ctrl_row, 2, 0);
    lv_obj_set_style_border_color(ctrl_row, CLR_BORDER, 0);
    lv_obj_set_style_radius(ctrl_row, 24, 0);
    lv_obj_set_style_pad_hor(ctrl_row, 20, 0);
    lv_obj_set_flex_flow(ctrl_row, LV_FLEX_FLOW_ROW);
    lv_obj_set_flex_align(ctrl_row, LV_FLEX_ALIGN_SPACE_BETWEEN, LV_FLEX_ALIGN_CENTER, LV_FLEX_ALIGN_CENTER);

    btn_temp_down = lv_btn_create(ctrl_row);
    lv_obj_set_size(btn_temp_down, 92, 92);
    lv_obj_set_style_radius(btn_temp_down, 22, 0);
    lv_obj_set_style_bg_color(btn_temp_down, CLR_BORDER, 0);
    lv_obj_add_event_cb(btn_temp_down, temp_down_btn_event_cb, LV_EVENT_CLICKED, NULL);
    lv_obj_t* lbl_dn = lv_label_create(btn_temp_down);
    lv_label_set_text(lbl_dn, LV_SYMBOL_MINUS);
    lv_obj_set_style_text_font(lbl_dn, &lv_font_montserrat_32, 0);
    lv_obj_set_style_text_color(lbl_dn, CLR_TEXT, 0);
    lv_obj_center(lbl_dn);

    lv_obj_t* target_col = lv_obj_create(ctrl_row);
    disableScroll(target_col);
    lv_obj_set_size(target_col, 220, 110);
    lv_obj_set_style_bg_opa(target_col, LV_OPA_TRANSP, 0);
    lv_obj_set_style_border_width(target_col, 0, 0);
    lv_obj_set_style_pad_all(target_col, 0, 0);
    lv_obj_set_flex_flow(target_col, LV_FLEX_FLOW_COLUMN);
    lv_obj_set_flex_align(target_col, LV_FLEX_ALIGN_CENTER, LV_FLEX_ALIGN_CENTER, LV_FLEX_ALIGN_CENTER);

    lbl_target_temp = lv_label_create(target_col);
    char tgt_buf[8];
    snprintf(tgt_buf, sizeof(tgt_buf), "%d\xc2\xb0", target_temperature);
    lv_label_set_text(lbl_target_temp, tgt_buf);
    lv_obj_set_style_text_font(lbl_target_temp, &lv_font_montserrat_48, 0);
    lv_obj_set_style_text_color(lbl_target_temp, CLR_ACCENT, 0);

    lv_obj_t* lbl_range = lv_label_create(target_col);
    lv_label_set_text(lbl_range, "range 25-65" "\xc2\xb0");
    lv_obj_set_style_text_font(lbl_range, &lv_font_montserrat_14, 0);
    lv_obj_set_style_text_color(lbl_range, CLR_SUBTEXT, 0);

    btn_temp_up = lv_btn_create(ctrl_row);
    lv_obj_set_size(btn_temp_up, 92, 92);
    lv_obj_set_style_radius(btn_temp_up, 22, 0);
    lv_obj_set_style_bg_color(btn_temp_up, CLR_ACCENT, 0);
    lv_obj_add_event_cb(btn_temp_up, temp_up_btn_event_cb, LV_EVENT_CLICKED, NULL);
    lv_obj_t* lbl_up = lv_label_create(btn_temp_up);
    lv_label_set_text(lbl_up, LV_SYMBOL_PLUS);
    lv_obj_set_style_text_font(lbl_up, &lv_font_montserrat_32, 0);
    lv_obj_set_style_text_color(lbl_up, lv_color_white(), 0);
    lv_obj_center(lbl_up);

    lv_obj_t* nav_row = lv_obj_create(body);
    disableScroll(nav_row);
    lv_obj_set_size(nav_row, lv_pct(100), 92);
    lv_obj_set_pos(nav_row, 0, 186);
    lv_obj_set_style_bg_opa(nav_row, LV_OPA_TRANSP, 0);
    lv_obj_set_style_border_width(nav_row, 0, 0);
    lv_obj_set_style_pad_all(nav_row, 0, 0);
    lv_obj_set_flex_flow(nav_row, LV_FLEX_FLOW_ROW);
    lv_obj_set_flex_align(nav_row, LV_FLEX_ALIGN_SPACE_BETWEEN, LV_FLEX_ALIGN_CENTER, LV_FLEX_ALIGN_CENTER);
    lv_obj_set_style_pad_column(nav_row, 16, 0);

    auto make_settings_nav_btn = [&](const char* icon, const char* text, lv_color_t fg, lv_event_cb_t cb) {
        lv_obj_t* btn = lv_btn_create(nav_row);
        disableScroll(btn);
        lv_obj_set_flex_grow(btn, 1);
        lv_obj_set_height(btn, 92);
        lv_obj_set_style_radius(btn, 20, 0);
        lv_obj_set_style_bg_color(btn, lv_color_white(), 0);
        lv_obj_set_style_border_width(btn, 2, 0);
        lv_obj_set_style_border_color(btn, CLR_BORDER, 0);
        lv_obj_set_style_shadow_width(btn, 0, 0);
        lv_obj_set_flex_flow(btn, LV_FLEX_FLOW_ROW);
        lv_obj_set_flex_align(btn, LV_FLEX_ALIGN_CENTER, LV_FLEX_ALIGN_CENTER, LV_FLEX_ALIGN_CENTER);
        lv_obj_set_style_pad_column(btn, 12, 0);
        lv_obj_add_event_cb(btn, cb, LV_EVENT_CLICKED, NULL);

        lv_obj_t* icon_lbl = lv_label_create(btn);
        lv_label_set_text(icon_lbl, icon);
        lv_obj_set_style_text_font(icon_lbl, &lv_font_montserrat_32, 0);
        lv_obj_set_style_text_color(icon_lbl, fg, 0);

        lv_obj_t* text_lbl = lv_label_create(btn);
        lv_label_set_text(text_lbl, text);
        lv_obj_set_style_text_font(text_lbl, &lv_font_montserrat_22, 0);
        lv_obj_set_style_text_color(text_lbl, fg, 0);
    };

    make_settings_nav_btn(LV_SYMBOL_LIST, "Schedule", CLR_ACCENT, goto_schedule_cb);
    make_settings_nav_btn(LV_SYMBOL_EDIT, "Diagnostics", CLR_SUBTEXT, goto_diagnostics_cb);
    make_settings_nav_btn(LV_SYMBOL_HOME, "Setup", CLR_ACCENT, goto_wizard_cb);

    // Demo / Real-time is a developer & presentation control — it now lives on
    // the Diagnostics (technician) screen, not on this consumer Settings screen.
}

static lv_obj_t* make_seg_btn(lv_obj_t* parent, const char* text, lv_event_cb_t cb, lv_obj_t** out_lbl) {
    lv_obj_t* btn = lv_btn_create(parent);
    lv_obj_set_flex_grow(btn, 1);
    lv_obj_set_style_radius(btn, 12, 0);
    lv_obj_set_style_shadow_width(btn, 0, 0);
    lv_obj_set_style_border_width(btn, 0, 0);
    lv_obj_add_event_cb(btn, cb, LV_EVENT_CLICKED, NULL);
    lv_obj_t* lbl = lv_label_create(btn);
    lv_label_set_text(lbl, text);
    lv_obj_set_style_text_font(lbl, &lv_font_montserrat_16, 0);
    lv_obj_center(lbl);
    if (out_lbl) *out_lbl = lbl;
    return btn;
}

static void build_schedule_page(lv_obj_t* scr) {
    page_schedule = lv_obj_create(scr);
    disableScroll(page_schedule);
    lv_obj_set_size(page_schedule, 800, 480);
    lv_obj_set_pos(page_schedule, 0, 0);
    lv_obj_set_style_bg_color(page_schedule, CLR_BG, 0);
    lv_obj_set_style_border_width(page_schedule, 0, 0);
    lv_obj_set_style_radius(page_schedule, 0, 0);
    lv_obj_set_style_pad_all(page_schedule, 0, 0);
    lv_obj_add_flag(page_schedule, LV_OBJ_FLAG_HIDDEN);

    lv_obj_t* header = make_header(page_schedule, CLR_TOPBAR);
    make_back_btn(header, page_settings);
    make_header_title(header, LV_SYMBOL_LIST "  Schedule");

    sched_body = lv_obj_create(page_schedule);
    disableScroll(sched_body);
    lv_obj_set_size(sched_body, 800, 416);
    lv_obj_set_pos(sched_body, 0, 64);
    lv_obj_set_style_bg_opa(sched_body, LV_OPA_TRANSP, 0);
    lv_obj_set_style_border_width(sched_body, 0, 0);
    lv_obj_set_style_pad_all(sched_body, 18, 0);
    lv_obj_set_flex_flow(sched_body, LV_FLEX_FLOW_ROW);
    lv_obj_set_flex_align(sched_body, LV_FLEX_ALIGN_START, LV_FLEX_ALIGN_START, LV_FLEX_ALIGN_START);
    lv_obj_set_style_pad_column(sched_body, 18, 0);

    // --- Left column: mode selector + Ready-by / Smart-learn panels ---
    lv_obj_t* left_col = lv_obj_create(sched_body);
    disableScroll(left_col);
    lv_obj_set_size(left_col, 372, lv_pct(100));
    lv_obj_set_style_bg_opa(left_col, LV_OPA_TRANSP, 0);
    lv_obj_set_style_border_width(left_col, 0, 0);
    lv_obj_set_style_pad_all(left_col, 0, 0);
    lv_obj_set_flex_flow(left_col, LV_FLEX_FLOW_COLUMN);
    lv_obj_set_style_pad_row(left_col, 14, 0);

    lv_obj_t* seg_mode = lv_obj_create(left_col);
    disableScroll(seg_mode);
    lv_obj_set_size(seg_mode, lv_pct(100), 64);
    lv_obj_set_style_bg_color(seg_mode, CLR_BORDER, 0);
    lv_obj_set_style_border_width(seg_mode, 0, 0);
    lv_obj_set_style_radius(seg_mode, 16, 0);
    lv_obj_set_style_pad_all(seg_mode, 5, 0);
    lv_obj_set_flex_flow(seg_mode, LV_FLEX_FLOW_ROW);
    lv_obj_set_style_pad_column(seg_mode, 6, 0);

    btn_mode_manual = make_seg_btn(seg_mode, "Manual",   sched_mode_manual_cb, &lbl_mode_manual);
    btn_mode_ready  = make_seg_btn(seg_mode, "Ready-by", sched_mode_ready_cb,  &lbl_mode_ready);
    btn_mode_smart  = make_seg_btn(seg_mode, "Smart",    sched_mode_smart_cb,  &lbl_mode_smart);

    // Ready-by panel
    panel_ready = lv_obj_create(left_col);
    disableScroll(panel_ready);
    lv_obj_set_size(panel_ready, lv_pct(100), 270);
    lv_obj_set_style_bg_opa(panel_ready, LV_OPA_TRANSP, 0);
    lv_obj_set_style_border_width(panel_ready, 0, 0);
    lv_obj_set_style_pad_all(panel_ready, 0, 0);
    lv_obj_set_flex_flow(panel_ready, LV_FLEX_FLOW_COLUMN);
    lv_obj_set_style_pad_row(panel_ready, 12, 0);

    lv_obj_t* seg_day = lv_obj_create(panel_ready);
    disableScroll(seg_day);
    lv_obj_set_size(seg_day, lv_pct(100), 54);
    lv_obj_set_style_bg_color(seg_day, lv_color_white(), 0);
    lv_obj_set_style_border_width(seg_day, 2, 0);
    lv_obj_set_style_border_color(seg_day, CLR_BORDER, 0);
    lv_obj_set_style_radius(seg_day, 14, 0);
    lv_obj_set_style_pad_all(seg_day, 5, 0);
    lv_obj_set_flex_flow(seg_day, LV_FLEX_FLOW_ROW);
    lv_obj_set_style_pad_column(seg_day, 6, 0);

    btn_day_wk = make_seg_btn(seg_day, "Sun-Thu", sched_day_wk_cb, &lbl_day_wk);   // Israeli work week
    btn_day_we = make_seg_btn(seg_day, "Fri-Sat", sched_day_we_cb, &lbl_day_we);   // Israeli weekend

    // Slot row: Morning/Evening selector + On/Off toggle for the selected slot
    lv_obj_t* slot_row = lv_obj_create(panel_ready);
    disableScroll(slot_row);
    lv_obj_set_size(slot_row, lv_pct(100), 48);
    lv_obj_set_style_bg_opa(slot_row, LV_OPA_TRANSP, 0);
    lv_obj_set_style_border_width(slot_row, 0, 0);
    lv_obj_set_style_pad_all(slot_row, 0, 0);
    lv_obj_set_flex_flow(slot_row, LV_FLEX_FLOW_ROW);
    lv_obj_set_flex_align(slot_row, LV_FLEX_ALIGN_START, LV_FLEX_ALIGN_CENTER, LV_FLEX_ALIGN_CENTER);
    lv_obj_set_style_pad_column(slot_row, 8, 0);

    lv_obj_t* seg_slot = lv_obj_create(slot_row);
    disableScroll(seg_slot);
    lv_obj_set_height(seg_slot, 48);
    lv_obj_set_flex_grow(seg_slot, 1);
    lv_obj_set_style_bg_color(seg_slot, lv_color_white(), 0);
    lv_obj_set_style_border_width(seg_slot, 2, 0);
    lv_obj_set_style_border_color(seg_slot, CLR_BORDER, 0);
    lv_obj_set_style_radius(seg_slot, 14, 0);
    lv_obj_set_style_pad_all(seg_slot, 5, 0);
    lv_obj_set_flex_flow(seg_slot, LV_FLEX_FLOW_ROW);
    lv_obj_set_style_pad_column(seg_slot, 6, 0);
    btn_slot_am = make_seg_btn(seg_slot, "Morning", sched_slot_am_cb, &lbl_slot_am);
    btn_slot_pm = make_seg_btn(seg_slot, "Evening", sched_slot_pm_cb, &lbl_slot_pm);

    btn_slot_en = lv_btn_create(slot_row);
    lv_obj_set_size(btn_slot_en, 96, 48);
    lv_obj_set_style_radius(btn_slot_en, 14, 0);
    lv_obj_set_style_border_width(btn_slot_en, 0, 0);
    lv_obj_add_event_cb(btn_slot_en, sched_slot_en_cb, LV_EVENT_CLICKED, NULL);
    lbl_slot_en = lv_label_create(btn_slot_en);
    lv_label_set_text(lbl_slot_en, LV_SYMBOL_OK "  On");
    lv_obj_set_style_text_font(lbl_slot_en, &lv_font_montserrat_16, 0);
    lv_obj_set_style_text_color(lbl_slot_en, lv_color_white(), 0);
    lv_obj_center(lbl_slot_en);

    lv_obj_t* time_card = lv_obj_create(panel_ready);
    disableScroll(time_card);
    lv_obj_set_size(time_card, lv_pct(100), 140);
    lv_obj_set_style_bg_color(time_card, lv_color_white(), 0);
    lv_obj_set_style_border_width(time_card, 2, 0);
    lv_obj_set_style_border_color(time_card, CLR_BORDER, 0);
    lv_obj_set_style_radius(time_card, 18, 0);
    lv_obj_set_flex_flow(time_card, LV_FLEX_FLOW_ROW);
    lv_obj_set_flex_align(time_card, LV_FLEX_ALIGN_SPACE_EVENLY, LV_FLEX_ALIGN_CENTER, LV_FLEX_ALIGN_CENTER);

    auto make_stepper = [&](lv_event_cb_t up_cb, lv_event_cb_t dn_cb, lv_obj_t** out_lbl) {
        lv_obj_t* col = lv_obj_create(time_card);
        disableScroll(col);
        lv_obj_set_size(col, 70, 120);
        lv_obj_set_style_bg_opa(col, LV_OPA_TRANSP, 0);
        lv_obj_set_style_border_width(col, 0, 0);
        lv_obj_set_style_pad_all(col, 0, 0);
        lv_obj_set_flex_flow(col, LV_FLEX_FLOW_COLUMN);
        lv_obj_set_flex_align(col, LV_FLEX_ALIGN_SPACE_BETWEEN, LV_FLEX_ALIGN_CENTER, LV_FLEX_ALIGN_CENTER);

        lv_obj_t* up = lv_btn_create(col);
        lv_obj_set_size(up, 64, 40);
        lv_obj_set_style_radius(up, 12, 0);
        lv_obj_set_style_bg_color(up, lv_color_hex(0xE3F2FD), 0);
        lv_obj_set_style_shadow_width(up, 0, 0);
        lv_obj_add_event_cb(up, up_cb, LV_EVENT_CLICKED, NULL);
        lv_obj_t* up_lbl = lv_label_create(up);
        lv_label_set_text(up_lbl, LV_SYMBOL_UP);
        lv_obj_set_style_text_color(up_lbl, CLR_ACCENT, 0);
        lv_obj_center(up_lbl);

        lv_obj_t* val = lv_label_create(col);
        lv_label_set_text(val, "00");
        lv_obj_set_style_text_font(val, &lv_font_montserrat_48, 0);
        if (out_lbl) *out_lbl = val;

        lv_obj_t* dn = lv_btn_create(col);
        lv_obj_set_size(dn, 64, 40);
        lv_obj_set_style_radius(dn, 12, 0);
        lv_obj_set_style_bg_color(dn, lv_color_hex(0xE3F2FD), 0);
        lv_obj_set_style_shadow_width(dn, 0, 0);
        lv_obj_add_event_cb(dn, dn_cb, LV_EVENT_CLICKED, NULL);
        lv_obj_t* dn_lbl = lv_label_create(dn);
        lv_label_set_text(dn_lbl, LV_SYMBOL_DOWN);
        lv_obj_set_style_text_color(dn_lbl, CLR_ACCENT, 0);
        lv_obj_center(dn_lbl);
    };

    make_stepper(sched_hh_up_cb, sched_hh_dn_cb, &lbl_hh);
    lv_obj_t* colon = lv_label_create(time_card);
    lv_label_set_text(colon, ":");
    lv_obj_set_style_text_font(colon, &lv_font_montserrat_42, 0);
    lv_obj_set_style_text_color(colon, CLR_SUBTEXT, 0);
    make_stepper(sched_mm_up_cb, sched_mm_dn_cb, &lbl_mm);

    // Smart-learn panel — learning status
    panel_smart = lv_obj_create(left_col);
    disableScroll(panel_smart);
    lv_obj_set_size(panel_smart, lv_pct(100), 220);
    lv_obj_set_style_bg_opa(panel_smart, LV_OPA_TRANSP, 0);
    lv_obj_set_style_border_width(panel_smart, 0, 0);
    lv_obj_set_style_pad_all(panel_smart, 0, 0);
    lv_obj_set_flex_flow(panel_smart, LV_FLEX_FLOW_COLUMN);
    lv_obj_set_style_pad_row(panel_smart, 10, 0);
    lv_obj_add_flag(panel_smart, LV_OBJ_FLAG_HIDDEN);

    lv_obj_t* learn_card = lv_obj_create(panel_smart);
    disableScroll(learn_card);
    lv_obj_set_size(learn_card, lv_pct(100), 130);
    lv_obj_set_style_bg_color(learn_card, lv_color_white(), 0);
    lv_obj_set_style_border_width(learn_card, 2, 0);
    lv_obj_set_style_border_color(learn_card, CLR_BORDER, 0);
    lv_obj_set_style_radius(learn_card, 18, 0);
    lv_obj_set_style_pad_all(learn_card, 16, 0);

    lv_obj_t* learn_title = lv_label_create(learn_card);
    lv_label_set_text(learn_title, "Learning your routine");
    lv_obj_set_style_text_font(learn_title, &lv_font_montserrat_18, 0);
    lv_obj_align(learn_title, LV_ALIGN_TOP_LEFT, 0, 0);

    lv_obj_t* learn_sub = lv_label_create(learn_card);
    lv_label_set_text(learn_sub, "Learning your shower times. Auto pre-heat begins after about 7 days of use.");
    lv_obj_set_style_text_font(learn_sub, &lv_font_montserrat_14, 0);
    lv_obj_set_style_text_color(learn_sub, CLR_SUBTEXT, 0);
    lv_obj_set_width(learn_sub, lv_pct(100));
    lv_label_set_long_mode(learn_sub, LV_LABEL_LONG_WRAP);
    lv_obj_align(learn_sub, LV_ALIGN_TOP_LEFT, 0, 26);

    lv_obj_t* learn_bar = lv_obj_create(learn_card);
    disableScroll(learn_bar);
    lv_obj_set_size(learn_bar, lv_pct(100), 14);
    lv_obj_align(learn_bar, LV_ALIGN_BOTTOM_LEFT, 0, 0);
    lv_obj_set_style_bg_color(learn_bar, CLR_BORDER, 0);
    lv_obj_set_style_border_width(learn_bar, 0, 0);
    lv_obj_set_style_radius(learn_bar, 7, 0);

    // Manual-mode panel — no auto pre-heat; user controls the boiler from Home.
    panel_manual = lv_obj_create(left_col);
    disableScroll(panel_manual);
    lv_obj_set_size(panel_manual, lv_pct(100), 220);
    lv_obj_set_style_bg_opa(panel_manual, LV_OPA_TRANSP, 0);
    lv_obj_set_style_border_width(panel_manual, 0, 0);
    lv_obj_set_style_pad_all(panel_manual, 0, 0);
    lv_obj_add_flag(panel_manual, LV_OBJ_FLAG_HIDDEN);

    lv_obj_t* manual_card = lv_obj_create(panel_manual);
    disableScroll(manual_card);
    lv_obj_set_size(manual_card, lv_pct(100), 130);
    lv_obj_set_style_bg_color(manual_card, lv_color_white(), 0);
    lv_obj_set_style_border_width(manual_card, 2, 0);
    lv_obj_set_style_border_color(manual_card, CLR_BORDER, 0);
    lv_obj_set_style_radius(manual_card, 18, 0);
    lv_obj_set_style_pad_all(manual_card, 16, 0);

    lv_obj_t* manual_title = lv_label_create(manual_card);
    lv_label_set_text(manual_title, "Manual control");
    lv_obj_set_style_text_font(manual_title, &lv_font_montserrat_18, 0);
    lv_obj_align(manual_title, LV_ALIGN_TOP_LEFT, 0, 0);

    lv_obj_t* manual_sub = lv_label_create(manual_card);
    lv_label_set_text(manual_sub, "No automatic pre-heat. Turn the boiler on or off yourself from the Home screen.");
    lv_obj_set_style_text_font(manual_sub, &lv_font_montserrat_14, 0);
    lv_obj_set_style_text_color(manual_sub, CLR_SUBTEXT, 0);
    lv_obj_set_width(manual_sub, lv_pct(100));
    lv_label_set_long_mode(manual_sub, LV_LABEL_LONG_WRAP);
    lv_obj_align(manual_sub, LV_ALIGN_TOP_LEFT, 0, 28);

    // --- Right column: next pre-heat estimate + skip-today ---
    lv_obj_t* right_col = lv_obj_create(sched_body);
    sched_right_col = right_col;
    disableScroll(right_col);
    lv_obj_set_size(right_col, 392, lv_pct(100));
    lv_obj_set_style_bg_opa(right_col, LV_OPA_TRANSP, 0);
    lv_obj_set_style_border_width(right_col, 0, 0);
    lv_obj_set_style_pad_all(right_col, 0, 0);
    lv_obj_set_flex_flow(right_col, LV_FLEX_FLOW_COLUMN);
    lv_obj_set_style_pad_row(right_col, 14, 0);

    lv_obj_t* next_card = lv_obj_create(right_col);
    disableScroll(next_card);
    lv_obj_set_size(next_card, lv_pct(100), 150);
    lv_obj_set_style_bg_color(next_card, lv_color_white(), 0);
    lv_obj_set_style_border_width(next_card, 2, 0);
    lv_obj_set_style_border_color(next_card, lv_color_hex(0xBBDEFB), 0);
    lv_obj_set_style_radius(next_card, 20, 0);
    lv_obj_set_style_pad_all(next_card, 20, 0);

    lv_obj_t* next_title = lv_label_create(next_card);
    lv_label_set_text(next_title, "Next auto pre-heat");
    lv_obj_set_style_text_font(next_title, &lv_font_montserrat_16, 0);
    lv_obj_set_style_text_color(next_title, CLR_SUBTEXT, 0);
    lv_obj_align(next_title, LV_ALIGN_TOP_LEFT, 0, 0);

    lbl_next_preheat = lv_label_create(next_card);
    lv_label_set_text(lbl_next_preheat, "06:45");
    lv_obj_set_style_text_font(lbl_next_preheat, &lv_font_montserrat_48, 0);
    lv_obj_set_style_text_color(lbl_next_preheat, CLR_ACCENT, 0);
    lv_obj_align(lbl_next_preheat, LV_ALIGN_TOP_LEFT, 0, 32);

    lv_obj_t* next_sub = lv_label_create(next_card);
    char lead_buf[52];
    snprintf(lead_buf, sizeof(lead_buf), "start adapts to water temp (~%d min typ.)", LEAD_TIME_MIN);
    lv_label_set_text(next_sub, lead_buf);
    lv_obj_set_style_text_font(next_sub, &lv_font_montserrat_14, 0);
    lv_obj_set_style_text_color(next_sub, CLR_SUBTEXT, 0);
    lv_obj_align(next_sub, LV_ALIGN_BOTTOM_LEFT, 0, 0);

    lv_obj_t* skip_btn = lv_btn_create(right_col);
    disableScroll(skip_btn);
    lv_obj_set_size(skip_btn, lv_pct(100), 66);
    lv_obj_set_style_radius(skip_btn, 18, 0);
    lv_obj_set_style_bg_color(skip_btn, lv_color_white(), 0);
    lv_obj_set_style_border_width(skip_btn, 2, 0);
    lv_obj_set_style_border_color(skip_btn, lv_color_hex(0xF0997B), 0);
    lv_obj_set_style_shadow_width(skip_btn, 0, 0);
    lv_obj_add_event_cb(skip_btn, sched_skip_cb, LV_EVENT_CLICKED, NULL);
    lbl_skip_btn = lv_label_create(skip_btn);
    lv_label_set_text(lbl_skip_btn, LV_SYMBOL_NEXT "  Skip auto today");
    lv_obj_set_style_text_font(lbl_skip_btn, &lv_font_montserrat_18, 0);
    lv_obj_set_style_text_color(lbl_skip_btn, lv_color_hex(0x993C1D), 0);
    lv_obj_center(lbl_skip_btn);

    update_mode_buttons();
    update_day_buttons();
    update_time_labels();
}

static void build_wizard_page(lv_obj_t* scr) {
    page_wizard = lv_obj_create(scr);
    disableScroll(page_wizard);
    lv_obj_set_size(page_wizard, 800, 480);
    lv_obj_set_pos(page_wizard, 0, 0);
    lv_obj_set_style_bg_color(page_wizard, CLR_BG, 0);
    lv_obj_set_style_border_width(page_wizard, 0, 0);
    lv_obj_set_style_radius(page_wizard, 0, 0);
    lv_obj_set_style_pad_all(page_wizard, 0, 0);
    lv_obj_add_flag(page_wizard, LV_OBJ_FLAG_HIDDEN);

    lv_obj_t* header = make_header(page_wizard, CLR_TOPBAR);
    make_back_btn(header, page_settings);
    make_header_title(header, LV_SYMBOL_HOME "  Setup Guide");

    lbl_wiz_progress = lv_label_create(page_wizard);
    lv_label_set_text(lbl_wiz_progress, "Step 1 of 3");
    lv_obj_set_style_text_font(lbl_wiz_progress, &lv_font_montserrat_16, 0);
    lv_obj_set_style_text_color(lbl_wiz_progress, CLR_SUBTEXT, 0);
    lv_obj_set_pos(lbl_wiz_progress, 22, 76);

    lv_obj_t* body = lv_obj_create(page_wizard);
    disableScroll(body);
    lv_obj_set_size(body, 800, 300);
    lv_obj_set_pos(body, 0, 106);
    lv_obj_set_style_bg_opa(body, LV_OPA_TRANSP, 0);
    lv_obj_set_style_border_width(body, 0, 0);
    lv_obj_set_style_pad_all(body, 22, 0);

    // ---- Step 1: Target temperature ----
    wiz_step_temp = lv_obj_create(body);
    disableScroll(wiz_step_temp);
    lv_obj_set_size(wiz_step_temp, lv_pct(100), lv_pct(100));
    lv_obj_set_pos(wiz_step_temp, 0, 0);
    lv_obj_set_style_bg_opa(wiz_step_temp, LV_OPA_TRANSP, 0);
    lv_obj_set_style_border_width(wiz_step_temp, 0, 0);
    lv_obj_set_style_pad_all(wiz_step_temp, 0, 0);

    lv_obj_t* t_title = lv_label_create(wiz_step_temp);
    lv_label_set_text(t_title, "What temperature do you want your water at, day to day?");
    lv_obj_set_style_text_font(t_title, &lv_font_montserrat_20, 0);
    lv_obj_set_style_text_color(t_title, CLR_TEXT, 0);
    lv_obj_set_width(t_title, lv_pct(100));
    lv_label_set_long_mode(t_title, LV_LABEL_LONG_WRAP);
    lv_obj_align(t_title, LV_ALIGN_TOP_MID, 0, 0);

    lv_obj_t* t_row = lv_obj_create(wiz_step_temp);
    disableScroll(t_row);
    lv_obj_set_size(t_row, 460, 130);
    lv_obj_align(t_row, LV_ALIGN_TOP_MID, 0, 80);
    lv_obj_set_style_bg_color(t_row, lv_color_white(), 0);
    lv_obj_set_style_border_width(t_row, 2, 0);
    lv_obj_set_style_border_color(t_row, CLR_BORDER, 0);
    lv_obj_set_style_radius(t_row, 24, 0);
    lv_obj_set_style_pad_hor(t_row, 20, 0);
    lv_obj_set_flex_flow(t_row, LV_FLEX_FLOW_ROW);
    lv_obj_set_flex_align(t_row, LV_FLEX_ALIGN_SPACE_BETWEEN, LV_FLEX_ALIGN_CENTER, LV_FLEX_ALIGN_CENTER);

    lv_obj_t* t_dn = lv_btn_create(t_row);
    lv_obj_set_size(t_dn, 92, 92);
    lv_obj_set_style_radius(t_dn, 22, 0);
    lv_obj_set_style_bg_color(t_dn, CLR_BORDER, 0);
    lv_obj_add_event_cb(t_dn, wiz_temp_dn_cb, LV_EVENT_CLICKED, NULL);
    lv_obj_t* t_dn_lbl = lv_label_create(t_dn);
    lv_label_set_text(t_dn_lbl, LV_SYMBOL_MINUS);
    lv_obj_set_style_text_font(t_dn_lbl, &lv_font_montserrat_32, 0);
    lv_obj_set_style_text_color(t_dn_lbl, CLR_TEXT, 0);
    lv_obj_center(t_dn_lbl);

    lbl_wiz_temp = lv_label_create(t_row);
    lv_label_set_text(lbl_wiz_temp, "60\xc2\xb0");
    lv_obj_set_style_text_font(lbl_wiz_temp, &lv_font_montserrat_48, 0);
    lv_obj_set_style_text_color(lbl_wiz_temp, CLR_ACCENT, 0);

    lv_obj_t* t_up = lv_btn_create(t_row);
    lv_obj_set_size(t_up, 92, 92);
    lv_obj_set_style_radius(t_up, 22, 0);
    lv_obj_set_style_bg_color(t_up, CLR_ACCENT, 0);
    lv_obj_add_event_cb(t_up, wiz_temp_up_cb, LV_EVENT_CLICKED, NULL);
    lv_obj_t* t_up_lbl = lv_label_create(t_up);
    lv_label_set_text(t_up_lbl, LV_SYMBOL_PLUS);
    lv_obj_set_style_text_font(t_up_lbl, &lv_font_montserrat_32, 0);
    lv_obj_set_style_text_color(t_up_lbl, lv_color_white(), 0);
    lv_obj_center(t_up_lbl);

    // ---- Step 2: Household size ----
    wiz_step_household = lv_obj_create(body);
    disableScroll(wiz_step_household);
    lv_obj_set_size(wiz_step_household, lv_pct(100), lv_pct(100));
    lv_obj_set_pos(wiz_step_household, 0, 0);
    lv_obj_set_style_bg_opa(wiz_step_household, LV_OPA_TRANSP, 0);
    lv_obj_set_style_border_width(wiz_step_household, 0, 0);
    lv_obj_set_style_pad_all(wiz_step_household, 0, 0);
    lv_obj_add_flag(wiz_step_household, LV_OBJ_FLAG_HIDDEN);

    lv_obj_t* h_title = lv_label_create(wiz_step_household);
    lv_label_set_text(h_title, "How many people use hot water daily?");
    lv_obj_set_style_text_font(h_title, &lv_font_montserrat_20, 0);
    lv_obj_set_style_text_color(h_title, CLR_TEXT, 0);
    lv_obj_set_width(h_title, lv_pct(100));
    lv_label_set_long_mode(h_title, LV_LABEL_LONG_WRAP);
    lv_obj_align(h_title, LV_ALIGN_TOP_MID, 0, 0);

    lv_obj_t* h_card = lv_obj_create(wiz_step_household);
    disableScroll(h_card);
    lv_obj_set_size(h_card, 220, 160);
    lv_obj_align(h_card, LV_ALIGN_TOP_MID, 0, 70);
    lv_obj_set_style_bg_color(h_card, lv_color_white(), 0);
    lv_obj_set_style_border_width(h_card, 2, 0);
    lv_obj_set_style_border_color(h_card, CLR_BORDER, 0);
    lv_obj_set_style_radius(h_card, 20, 0);
    lv_obj_set_flex_flow(h_card, LV_FLEX_FLOW_ROW);
    lv_obj_set_flex_align(h_card, LV_FLEX_ALIGN_CENTER, LV_FLEX_ALIGN_CENTER, LV_FLEX_ALIGN_CENTER);
    make_value_stepper(h_card, wiz_household_up_cb, wiz_household_dn_cb, &lbl_wiz_household);

    // ---- Step 3: Ready-by time ----
    wiz_step_schedule = lv_obj_create(body);
    disableScroll(wiz_step_schedule);
    lv_obj_set_size(wiz_step_schedule, lv_pct(100), lv_pct(100));
    lv_obj_set_pos(wiz_step_schedule, 0, 0);
    lv_obj_set_style_bg_opa(wiz_step_schedule, LV_OPA_TRANSP, 0);
    lv_obj_set_style_border_width(wiz_step_schedule, 0, 0);
    lv_obj_set_style_pad_all(wiz_step_schedule, 0, 0);
    lv_obj_add_flag(wiz_step_schedule, LV_OBJ_FLAG_HIDDEN);

    lv_obj_t* s_title = lv_label_create(wiz_step_schedule);
    lv_label_set_text(s_title, "What time should hot water be ready by, by default?");
    lv_obj_set_style_text_font(s_title, &lv_font_montserrat_20, 0);
    lv_obj_set_style_text_color(s_title, CLR_TEXT, 0);
    lv_obj_set_width(s_title, lv_pct(100));
    lv_label_set_long_mode(s_title, LV_LABEL_LONG_WRAP);
    lv_obj_align(s_title, LV_ALIGN_TOP_MID, 0, 0);

    lv_obj_t* s_card = lv_obj_create(wiz_step_schedule);
    disableScroll(s_card);
    lv_obj_set_size(s_card, 260, 160);
    lv_obj_align(s_card, LV_ALIGN_TOP_MID, 0, 70);
    lv_obj_set_style_bg_color(s_card, lv_color_white(), 0);
    lv_obj_set_style_border_width(s_card, 2, 0);
    lv_obj_set_style_border_color(s_card, CLR_BORDER, 0);
    lv_obj_set_style_radius(s_card, 20, 0);
    lv_obj_set_flex_flow(s_card, LV_FLEX_FLOW_ROW);
    lv_obj_set_flex_align(s_card, LV_FLEX_ALIGN_SPACE_EVENLY, LV_FLEX_ALIGN_CENTER, LV_FLEX_ALIGN_CENTER);

    make_value_stepper(s_card, wiz_hh_up_cb, wiz_hh_dn_cb, &lbl_wiz_hh);
    lv_obj_t* colon = lv_label_create(s_card);
    lv_label_set_text(colon, ":");
    lv_obj_set_style_text_font(colon, &lv_font_montserrat_42, 0);
    lv_obj_set_style_text_color(colon, CLR_SUBTEXT, 0);
    make_value_stepper(s_card, wiz_mm_up_cb, wiz_mm_dn_cb, &lbl_wiz_mm);

    // ---- Footer nav (Back / Next-Finish) ----
    btn_wiz_back = lv_btn_create(page_wizard);
    lv_obj_set_size(btn_wiz_back, 140, 56);
    lv_obj_set_pos(btn_wiz_back, 22, 406);
    lv_obj_set_style_radius(btn_wiz_back, 16, 0);
    lv_obj_set_style_bg_color(btn_wiz_back, lv_color_white(), 0);
    lv_obj_set_style_border_width(btn_wiz_back, 2, 0);
    lv_obj_set_style_border_color(btn_wiz_back, CLR_BORDER, 0);
    lv_obj_set_style_shadow_width(btn_wiz_back, 0, 0);
    lv_obj_add_event_cb(btn_wiz_back, wizard_back_cb, LV_EVENT_CLICKED, NULL);
    lv_obj_add_flag(btn_wiz_back, LV_OBJ_FLAG_HIDDEN);
    lv_obj_t* back_lbl = lv_label_create(btn_wiz_back);
    lv_label_set_text(back_lbl, LV_SYMBOL_LEFT "  Back");
    lv_obj_set_style_text_font(back_lbl, &lv_font_montserrat_18, 0);
    lv_obj_set_style_text_color(back_lbl, CLR_TEXT, 0);
    lv_obj_center(back_lbl);

    btn_wiz_next = lv_btn_create(page_wizard);
    lv_obj_set_size(btn_wiz_next, 180, 56);
    lv_obj_set_pos(btn_wiz_next, 598, 406);
    lv_obj_set_style_radius(btn_wiz_next, 16, 0);
    lv_obj_set_style_bg_color(btn_wiz_next, CLR_ACCENT, 0);
    lv_obj_set_style_border_width(btn_wiz_next, 0, 0);
    lv_obj_add_event_cb(btn_wiz_next, wizard_next_cb, LV_EVENT_CLICKED, NULL);
    lbl_wiz_next_text = lv_label_create(btn_wiz_next);
    lv_label_set_text(lbl_wiz_next_text, "Next");
    lv_obj_set_style_text_font(lbl_wiz_next_text, &lv_font_montserrat_18, 0);
    lv_obj_set_style_text_color(lbl_wiz_next_text, lv_color_white(), 0);
    lv_obj_center(lbl_wiz_next_text);
}

static void build_network_page(lv_obj_t* scr) {
    page_network = lv_obj_create(scr);
    disableScroll(page_network);
    lv_obj_set_size(page_network, 800, 480);
    lv_obj_set_pos(page_network, 0, 0);
    lv_obj_set_style_bg_color(page_network, CLR_BG, 0);
    lv_obj_set_style_border_width(page_network, 0, 0);
    lv_obj_set_style_radius(page_network, 0, 0);
    lv_obj_set_style_pad_all(page_network, 0, 0);
    lv_obj_add_flag(page_network, LV_OBJ_FLAG_HIDDEN);

    lv_obj_t* header = make_header(page_network, CLR_TOPBAR);
    make_back_btn(header, page_home);
    make_header_title(header, LV_SYMBOL_WIFI "  Network");

    lv_obj_t* scan_btn = lv_btn_create(header);
    lv_obj_set_width(scan_btn, LV_SIZE_CONTENT);
    lv_obj_set_height(scan_btn, 48);
    lv_obj_set_style_radius(scan_btn, 12, 0);
    lv_obj_set_style_bg_color(scan_btn, lv_color_white(), 0);
    lv_obj_set_style_bg_opa(scan_btn, LV_OPA_30, 0);
    lv_obj_set_style_border_width(scan_btn, 0, 0);
    lv_obj_set_style_pad_hor(scan_btn, 20, 0);
    lv_obj_add_event_cb(scan_btn, net_scan_btn_cb, LV_EVENT_CLICKED, NULL);
    lv_obj_t* scan_lbl = lv_label_create(scan_btn);
    lv_label_set_text(scan_lbl, LV_SYMBOL_REFRESH "  Scan");
    lv_obj_set_style_text_font(scan_lbl, &lv_font_montserrat_18, 0);
    lv_obj_set_style_text_color(scan_lbl, lv_color_white(), 0);
    lv_obj_center(scan_lbl);

    lbl_net_status = lv_label_create(page_network);
    lv_label_set_text(lbl_net_status, LV_SYMBOL_WARNING "  Not connected");
    lv_obj_set_style_text_font(lbl_net_status, &lv_font_montserrat_18, 0);
    lv_obj_set_style_text_color(lbl_net_status, lv_palette_main(LV_PALETTE_RED), 0);
    lv_obj_set_pos(lbl_net_status, 18, 74);

    net_list_container = lv_obj_create(page_network);
    lv_obj_set_size(net_list_container, 764, 330);
    lv_obj_set_pos(net_list_container, 18, 112);
    lv_obj_set_style_bg_opa(net_list_container, LV_OPA_TRANSP, 0);
    lv_obj_set_style_border_width(net_list_container, 0, 0);
    lv_obj_set_style_pad_all(net_list_container, 0, 0);
    lv_obj_set_flex_flow(net_list_container, LV_FLEX_FLOW_COLUMN);
    lv_obj_set_style_pad_row(net_list_container, 10, 0);
}

static void build_password_page(lv_obj_t* scr) {
    page_password = lv_obj_create(scr);
    disableScroll(page_password);
    lv_obj_set_size(page_password, 800, 480);
    lv_obj_set_pos(page_password, 0, 0);
    lv_obj_set_style_bg_color(page_password, CLR_BG, 0);
    lv_obj_set_style_border_width(page_password, 0, 0);
    lv_obj_set_style_radius(page_password, 0, 0);
    lv_obj_set_style_pad_all(page_password, 0, 0);
    lv_obj_add_flag(page_password, LV_OBJ_FLAG_HIDDEN);

    lv_obj_t* header = make_header(page_password, CLR_TOPBAR);
    lv_obj_set_size(header, 800, 60);
    make_back_btn(header, page_network);
    lbl_pwd_title = make_header_title(header, "Connect");
    lv_obj_set_style_text_font(lbl_pwd_title, &lv_font_montserrat_22, 0);

    lv_obj_t* field_row = lv_obj_create(page_password);
    disableScroll(field_row);
    lv_obj_set_size(field_row, 776, 58);
    lv_obj_set_pos(field_row, 12, 70);
    lv_obj_set_style_bg_opa(field_row, LV_OPA_TRANSP, 0);
    lv_obj_set_style_border_width(field_row, 0, 0);
    lv_obj_set_style_pad_all(field_row, 0, 0);
    lv_obj_set_flex_flow(field_row, LV_FLEX_FLOW_ROW);
    lv_obj_set_flex_align(field_row, LV_FLEX_ALIGN_START, LV_FLEX_ALIGN_CENTER, LV_FLEX_ALIGN_CENTER);
    lv_obj_set_style_pad_column(field_row, 10, 0);

    password_textarea = lv_textarea_create(field_row);
    lv_obj_set_flex_grow(password_textarea, 1);
    lv_obj_set_height(password_textarea, 52);
    lv_textarea_set_one_line(password_textarea, true);
    lv_textarea_set_password_mode(password_textarea, true);
    lv_textarea_set_placeholder_text(password_textarea, "Enter password");
    lv_obj_set_style_text_font(password_textarea, &lv_font_montserrat_20, 0);
    lv_obj_set_style_border_color(password_textarea, CLR_ACCENT, 0);
    lv_obj_set_style_radius(password_textarea, 12, 0);

    lv_obj_t* eye_btn = lv_btn_create(field_row);
    lv_obj_set_size(eye_btn, 50, 50);
    lv_obj_set_style_radius(eye_btn, 10, 0);
    lv_obj_set_style_bg_color(eye_btn, lv_color_hex(0xE8F0FE), 0);
    lv_obj_set_style_shadow_width(eye_btn, 0, 0);
    lv_obj_add_event_cb(eye_btn, pwd_eye_toggle_cb, LV_EVENT_CLICKED, NULL);
    lbl_eye_icon = lv_label_create(eye_btn);
    lv_label_set_text(lbl_eye_icon, LV_SYMBOL_EYE_CLOSE);
    lv_obj_set_style_text_color(lbl_eye_icon, CLR_ACCENT, 0);
    lv_obj_center(lbl_eye_icon);

    btn_connect = lv_btn_create(field_row);
    lv_obj_set_size(btn_connect, 130, 52);
    lv_obj_set_style_radius(btn_connect, 12, 0);
    lv_obj_set_style_bg_color(btn_connect, CLR_ON, 0);
    lv_obj_set_style_shadow_width(btn_connect, 0, 0);
    lv_obj_add_event_cb(btn_connect, pwd_connect_btn_cb, LV_EVENT_CLICKED, NULL);
    lbl_connect_btn_text = lv_label_create(btn_connect);
    lv_label_set_text(lbl_connect_btn_text, "Connect");
    lv_obj_set_style_text_font(lbl_connect_btn_text, &lv_font_montserrat_18, 0);
    lv_obj_set_style_text_color(lbl_connect_btn_text, lv_color_white(), 0);
    lv_obj_center(lbl_connect_btn_text);

    lbl_pwd_error = lv_label_create(page_password);
    lv_label_set_text(lbl_pwd_error, "");
    lv_obj_set_style_text_font(lbl_pwd_error, &lv_font_montserrat_14, 0);
    lv_obj_set_style_text_color(lbl_pwd_error, lv_palette_main(LV_PALETTE_RED), 0);
    lv_obj_set_pos(lbl_pwd_error, 12, 130);

    keyboard = lv_keyboard_create(page_password);
    lv_obj_set_size(keyboard, 800, 280);
    lv_obj_align(keyboard, LV_ALIGN_BOTTOM_MID, 0, 0);
    lv_keyboard_set_textarea(keyboard, password_textarea);

    // Post-connect "save password?" modal — replaces the old pre-connect checkbox
    save_modal = lv_obj_create(page_password);
    disableScroll(save_modal);
    lv_obj_set_size(save_modal, 800, 480);
    lv_obj_set_pos(save_modal, 0, 0);
    lv_obj_set_style_bg_color(save_modal, lv_color_hex(0x0A0C14), 0);
    lv_obj_set_style_bg_opa(save_modal, LV_OPA_50, 0);
    lv_obj_set_style_border_width(save_modal, 0, 0);
    lv_obj_set_style_radius(save_modal, 0, 0);
    lv_obj_add_flag(save_modal, LV_OBJ_FLAG_HIDDEN);

    lv_obj_t* modal_card = lv_obj_create(save_modal);
    disableScroll(modal_card);
    lv_obj_set_size(modal_card, 480, 260);
    lv_obj_center(modal_card);
    lv_obj_set_style_bg_color(modal_card, lv_color_white(), 0);
    lv_obj_set_style_radius(modal_card, 24, 0);
    lv_obj_set_style_pad_all(modal_card, 24, 0);

    lv_obj_t* modal_title = lv_label_create(modal_card);
    lv_label_set_text(modal_title, "Connected");
    lv_obj_set_style_text_font(modal_title, &lv_font_montserrat_24, 0);
    lv_obj_align(modal_title, LV_ALIGN_TOP_MID, 0, 0);

    lbl_save_modal_ssid = lv_label_create(modal_card);
    lv_label_set_text(lbl_save_modal_ssid, "");
    lv_obj_set_style_text_font(lbl_save_modal_ssid, &lv_font_montserrat_16, 0);
    lv_obj_set_style_text_color(lbl_save_modal_ssid, CLR_SUBTEXT, 0);
    lv_obj_align(lbl_save_modal_ssid, LV_ALIGN_TOP_MID, 0, 34);

    lv_obj_t* modal_sub = lv_label_create(modal_card);
    lv_label_set_text(modal_sub, "Save this password so you won't\nneed to type it again next time?");
    lv_obj_set_style_text_font(modal_sub, &lv_font_montserrat_16, 0);
    lv_obj_set_style_text_align(modal_sub, LV_TEXT_ALIGN_CENTER, 0);
    lv_obj_align(modal_sub, LV_ALIGN_TOP_MID, 0, 64);

    lv_obj_t* modal_btn_row = lv_obj_create(modal_card);
    disableScroll(modal_btn_row);
    lv_obj_set_size(modal_btn_row, lv_pct(100), 64);
    lv_obj_align(modal_btn_row, LV_ALIGN_BOTTOM_MID, 0, 0);
    lv_obj_set_style_bg_opa(modal_btn_row, LV_OPA_TRANSP, 0);
    lv_obj_set_style_border_width(modal_btn_row, 0, 0);
    lv_obj_set_style_pad_all(modal_btn_row, 0, 0);
    lv_obj_set_flex_flow(modal_btn_row, LV_FLEX_FLOW_ROW);
    lv_obj_set_flex_align(modal_btn_row, LV_FLEX_ALIGN_SPACE_BETWEEN, LV_FLEX_ALIGN_CENTER, LV_FLEX_ALIGN_CENTER);
    lv_obj_set_style_pad_column(modal_btn_row, 14, 0);

    lv_obj_t* btn_not_now = lv_btn_create(modal_btn_row);
    lv_obj_set_flex_grow(btn_not_now, 1);
    lv_obj_set_height(btn_not_now, 64);
    lv_obj_set_style_radius(btn_not_now, 16, 0);
    lv_obj_set_style_bg_color(btn_not_now, lv_color_white(), 0);
    lv_obj_set_style_border_width(btn_not_now, 2, 0);
    lv_obj_set_style_border_color(btn_not_now, lv_color_hex(0xCFD8DC), 0);
    lv_obj_set_style_shadow_width(btn_not_now, 0, 0);
    lv_obj_add_event_cb(btn_not_now, save_modal_no_cb, LV_EVENT_CLICKED, NULL);
    lv_obj_t* lbl_not_now = lv_label_create(btn_not_now);
    lv_label_set_text(lbl_not_now, "Not now");
    lv_obj_set_style_text_color(lbl_not_now, lv_color_hex(0x546E7A), 0);
    lv_obj_center(lbl_not_now);

    lv_obj_t* btn_save = lv_btn_create(modal_btn_row);
    lv_obj_set_flex_grow(btn_save, 1);
    lv_obj_set_height(btn_save, 64);
    lv_obj_set_style_radius(btn_save, 16, 0);
    lv_obj_set_style_bg_color(btn_save, CLR_ON, 0);
    lv_obj_set_style_shadow_width(btn_save, 0, 0);
    lv_obj_add_event_cb(btn_save, save_modal_yes_cb, LV_EVENT_CLICKED, NULL);
    lv_obj_t* lbl_save = lv_label_create(btn_save);
    lv_label_set_text(lbl_save, LV_SYMBOL_SAVE "  Save");
    lv_obj_set_style_text_color(lbl_save, lv_color_white(), 0);
    lv_obj_center(lbl_save);
}

static void build_stats_page(lv_obj_t* scr) {
    page_stats = lv_obj_create(scr);
    disableScroll(page_stats);
    lv_obj_set_size(page_stats, 800, 480);
    lv_obj_set_pos(page_stats, 0, 0);
    lv_obj_set_style_bg_color(page_stats, CLR_BG, 0);
    lv_obj_set_style_border_width(page_stats, 0, 0);
    lv_obj_set_style_radius(page_stats, 0, 0);
    lv_obj_set_style_pad_all(page_stats, 0, 0);
    lv_obj_add_flag(page_stats, LV_OBJ_FLAG_HIDDEN);

    lv_obj_t* header = make_header(page_stats, CLR_TOPBAR);
    make_back_btn(header, page_home);
    make_header_title(header, LV_SYMBOL_BARS "  Stats");

    lv_obj_t* row1 = lv_obj_create(page_stats);
    disableScroll(row1);
    lv_obj_set_size(row1, 768, 100);
    lv_obj_set_pos(row1, 16, 80);
    lv_obj_set_style_bg_opa(row1, LV_OPA_TRANSP, 0);
    lv_obj_set_style_border_width(row1, 0, 0);
    lv_obj_set_style_pad_all(row1, 0, 0);
    lv_obj_set_flex_flow(row1, LV_FLEX_FLOW_ROW);
    lv_obj_set_style_pad_column(row1, 12, 0);

    lbl_system_mode = make_stat_card(row1, "System Mode", CLR_ACCENT);
    lv_obj_set_style_text_font(lbl_system_mode, &lv_font_montserrat_20, 0);
    lv_obj_set_width(lbl_system_mode, 150);
    lv_label_set_long_mode(lbl_system_mode, LV_LABEL_LONG_DOT);
    lbl_stat_power  = make_stat_card(row1, "Power now", lv_palette_main(LV_PALETTE_ORANGE));
    lbl_stat_flow   = make_stat_card(row1, "Flow now", CLR_ACCENT);
    lbl_stat_plc    = make_stat_card(row1, "Communication", lv_palette_main(LV_PALETTE_RED));

    lv_obj_t* progress_card = lv_obj_create(page_stats);
    disableScroll(progress_card);
    lv_obj_set_size(progress_card, 768, 220);
    lv_obj_set_pos(progress_card, 16, 196);
    lv_obj_set_style_bg_color(progress_card, lv_color_white(), 0);
    lv_obj_set_style_border_width(progress_card, 2, 0);
    lv_obj_set_style_border_color(progress_card, CLR_BORDER, 0);
    lv_obj_set_style_radius(progress_card, 18, 0);
    lv_obj_set_style_pad_all(progress_card, 18, 0);

    lv_obj_t* usage_title = lv_label_create(progress_card);
    lv_label_set_text(usage_title, "Water Usage - last 24h");
    lv_obj_set_style_text_font(usage_title, &lv_font_montserrat_18, 0);
    lv_obj_align(usage_title, LV_ALIGN_TOP_LEFT, 0, 0);

    lbl_usage_today = lv_label_create(progress_card);
    lv_label_set_text(lbl_usage_today, "Today: -- L");
    lv_obj_set_style_text_font(lbl_usage_today, &lv_font_montserrat_18, 0);
    lv_obj_set_style_text_color(lbl_usage_today, CLR_SUBTEXT, 0);
    lv_obj_align(lbl_usage_today, LV_ALIGN_TOP_RIGHT, 0, 0);

    // Bar color encodes that hour's tank temperature (pale blue = cool,
    // deep red = hot) via usage_chart_draw_event_cb; bar height is liters.
    // LVGL draws axis tick labels *outside* the chart's own box (to the
    // left of it for Y, below it for X) rather than shrinking the plot
    // area to fit them, so the chart itself is sized smaller than the
    // card and offset, leaving blank margin on the left/bottom for them
    // to render into instead of being clipped by the card's edge.
    chart_usage = lv_chart_create(progress_card);
    lv_obj_set_pos(chart_usage, 44, 32);
    lv_obj_set_size(chart_usage, 678, 126);
    lv_obj_set_style_bg_opa(chart_usage, LV_OPA_TRANSP, LV_PART_MAIN);
    lv_obj_set_style_border_width(chart_usage, 0, LV_PART_MAIN);
    lv_obj_set_style_text_font(chart_usage, &lv_font_montserrat_14, LV_PART_TICKS);
    lv_obj_set_style_text_color(chart_usage, CLR_SUBTEXT, LV_PART_TICKS);
    lv_obj_set_style_pad_left(chart_usage, 4, LV_PART_TICKS);
    lv_obj_set_style_pad_bottom(chart_usage, 4, LV_PART_TICKS);
    lv_chart_set_type(chart_usage, LV_CHART_TYPE_BAR);
    lv_chart_set_point_count(chart_usage, USAGE_HOURS);
    lv_chart_set_range(chart_usage, LV_CHART_AXIS_PRIMARY_Y, 0, 60);
    lv_chart_set_div_line_count(chart_usage, 4, 5);   // vdiv=1 divides by zero in LVGL's div-line draw code
    lv_chart_set_axis_tick(chart_usage, LV_CHART_AXIS_PRIMARY_Y, 6, 3, 4, 1, true, 34);   // 0/20/40/60 L
    lv_chart_set_axis_tick(chart_usage, LV_CHART_AXIS_PRIMARY_X, 6, 3, 5, 1, true, 26);   // 00/06/12/18/24
    ser_usage = lv_chart_add_series(chart_usage, CLR_ACCENT, LV_CHART_AXIS_PRIMARY_Y);
    for (int i = 0; i < USAGE_HOURS; i++) lv_chart_set_value_by_id(chart_usage, ser_usage, i, 0);
    lv_obj_add_event_cb(chart_usage, usage_chart_draw_event_cb, LV_EVENT_DRAW_PART_BEGIN, NULL);
    lv_obj_add_event_cb(chart_usage, hourly_chart_x_tick_cb, LV_EVENT_DRAW_PART_BEGIN, NULL);
}

static void build_solar_page(lv_obj_t* scr) {
    page_solar = lv_obj_create(scr);
    disableScroll(page_solar);
    lv_obj_set_size(page_solar, 800, 480);
    lv_obj_set_pos(page_solar, 0, 0);
    lv_obj_set_style_bg_color(page_solar, CLR_BG, 0);
    lv_obj_set_style_border_width(page_solar, 0, 0);
    lv_obj_set_style_radius(page_solar, 0, 0);
    lv_obj_set_style_pad_all(page_solar, 0, 0);
    lv_obj_add_flag(page_solar, LV_OBJ_FLAG_HIDDEN);

    lv_obj_t* header = make_header(page_solar, CLR_TOPBAR);
    make_back_btn(header, page_home);
    make_header_title(header, LV_SYMBOL_IMAGE "  Solar Forecast");

    lv_obj_t* card = lv_obj_create(page_solar);
    disableScroll(card);
    lv_obj_set_size(card, 768, 380);
    lv_obj_set_pos(card, 16, 80);
    lv_obj_set_style_bg_color(card, lv_color_white(), 0);
    lv_obj_set_style_border_width(card, 2, 0);
    lv_obj_set_style_border_color(card, CLR_BORDER, 0);
    lv_obj_set_style_radius(card, 18, 0);
    lv_obj_set_style_pad_all(card, 18, 0);

    lv_obj_t* title = lv_label_create(card);
    lv_label_set_text(title, "Solar Irradiance - today (W/m2)");
    lv_obj_set_style_text_font(title, &lv_font_montserrat_18, 0);
    lv_obj_align(title, LV_ALIGN_TOP_LEFT, 0, 0);

    lbl_solar_peak = lv_label_create(card);
    lv_label_set_text(lbl_solar_peak, "Peak: -- W/m2");
    lv_obj_set_style_text_font(lbl_solar_peak, &lv_font_montserrat_18, 0);
    lv_obj_set_style_text_color(lbl_solar_peak, CLR_SUBTEXT, 0);
    lv_obj_align(lbl_solar_peak, LV_ALIGN_TOP_RIGHT, 0, 0);

    // Global horizontal irradiance (shortwave_radiation) as a smooth curve —
    // it rises/falls continuously through the day, so a line reads more
    // naturally here than the discrete-event bars used for water usage.
    // See the comment above chart_usage: axis labels draw outside the
    // chart's own box, so it's sized smaller than the card and offset to
    // leave blank margin for them instead of being clipped by the card edge.
    chart_solar = lv_chart_create(card);
    lv_obj_set_pos(chart_solar, 50, 34);
    lv_obj_set_size(chart_solar, 670, 284);
    lv_obj_set_style_bg_opa(chart_solar, LV_OPA_TRANSP, LV_PART_MAIN);
    lv_obj_set_style_border_width(chart_solar, 0, LV_PART_MAIN);
    lv_obj_set_style_size(chart_solar, 0, LV_PART_INDICATOR);   // hide point markers
    lv_obj_set_style_text_font(chart_solar, &lv_font_montserrat_14, LV_PART_TICKS);
    lv_obj_set_style_text_color(chart_solar, CLR_SUBTEXT, LV_PART_TICKS);
    lv_obj_set_style_pad_left(chart_solar, 4, LV_PART_TICKS);
    lv_obj_set_style_pad_bottom(chart_solar, 4, LV_PART_TICKS);
    lv_chart_set_type(chart_solar, LV_CHART_TYPE_LINE);
    lv_chart_set_point_count(chart_solar, SOLAR_HOURS);
    lv_chart_set_range(chart_solar, LV_CHART_AXIS_PRIMARY_Y, 0, 1000);
    lv_chart_set_div_line_count(chart_solar, 4, 6);
    lv_chart_set_axis_tick(chart_solar, LV_CHART_AXIS_PRIMARY_Y, 6, 3, 5, 1, true, 44);   // 0/250/500/750/1000 W/m2
    lv_chart_set_axis_tick(chart_solar, LV_CHART_AXIS_PRIMARY_X, 6, 3, 5, 1, true, 26);   // 00/06/12/18/24
    ser_solar = lv_chart_add_series(chart_solar, lv_color_hex(0xF57F17), LV_CHART_AXIS_PRIMARY_Y);
    for (int i = 0; i < SOLAR_HOURS; i++) lv_chart_set_value_by_id(chart_solar, ser_solar, i, 0);
    lv_obj_add_event_cb(chart_solar, hourly_chart_x_tick_cb, LV_EVENT_DRAW_PART_BEGIN, NULL);
}

static void build_diagnostics_page(lv_obj_t* scr) {
    page_diagnostics = lv_obj_create(scr);
    disableScroll(page_diagnostics);
    lv_obj_set_size(page_diagnostics, 800, 480);
    lv_obj_set_pos(page_diagnostics, 0, 0);
    lv_obj_set_style_bg_color(page_diagnostics, lv_color_hex(0x1B2226), 0);
    lv_obj_set_style_border_width(page_diagnostics, 0, 0);
    lv_obj_set_style_radius(page_diagnostics, 0, 0);
    lv_obj_set_style_pad_all(page_diagnostics, 0, 0);
    lv_obj_add_flag(page_diagnostics, LV_OBJ_FLAG_HIDDEN);

    lv_obj_t* header = make_header(page_diagnostics, CLR_DIAG_HDR);
    make_back_btn(header, page_settings);
    make_header_title(header, LV_SYMBOL_EDIT "  Diagnostics");

    // Data source (Demo / Real-time) — dev & presentation control. Lives on the
    // Diagnostics (technician) screen, not on the consumer Settings screen.
    // DEMO = mock scenario data; REAL-TIME = live DS18B20 / YF-B6 / ACS758.
    btn_app_mode = lv_btn_create(header);
    lv_obj_set_height(btn_app_mode, 40);
    lv_obj_set_width(btn_app_mode, LV_SIZE_CONTENT);
    lv_obj_align(btn_app_mode, LV_ALIGN_RIGHT_MID, -16, 0);
    lv_obj_set_style_radius(btn_app_mode, 12, 0);
    lv_obj_set_style_bg_color(btn_app_mode, appMode == MODE_DEMO ? CLR_WAITING : CLR_ON, 0);
    lv_obj_set_style_border_width(btn_app_mode, 0, 0);
    lv_obj_add_event_cb(btn_app_mode, mode_toggle_cb, LV_EVENT_CLICKED, NULL);
    lbl_app_mode = lv_label_create(btn_app_mode);
    lv_label_set_text(lbl_app_mode,
                      appMode == MODE_DEMO ? LV_SYMBOL_PLAY "  Data: Demo"
                                           : LV_SYMBOL_EYE_OPEN "  Data: Real-time");
    lv_obj_set_style_text_font(lbl_app_mode, &lv_font_montserrat_16, 0);
    lv_obj_set_style_text_color(lbl_app_mode, lv_color_white(), 0);
    lv_obj_center(lbl_app_mode);

    lv_obj_t* grid = lv_obj_create(page_diagnostics);
    disableScroll(grid);
    lv_obj_set_size(grid, 768, 396);
    lv_obj_set_pos(grid, 16, 70);
    lv_obj_set_style_bg_opa(grid, LV_OPA_TRANSP, 0);
    lv_obj_set_style_border_width(grid, 0, 0);
    lv_obj_set_style_pad_all(grid, 0, 0);
    static lv_coord_t col_dsc[] = {248, 248, 248, LV_GRID_TEMPLATE_LAST};
    static lv_coord_t row_dsc[] = {88, 88, 88, 88, LV_GRID_TEMPLATE_LAST};
    lv_obj_set_grid_dsc_array(grid, col_dsc, row_dsc);
    lv_obj_set_layout(grid, LV_LAYOUT_GRID);
    lv_obj_set_style_pad_column(grid, 12, 0);
    lv_obj_set_style_pad_row(grid, 10, 0);

    auto place = [&](lv_obj_t* card_value_owner, int col, int col_span, int row) {
        lv_obj_t* card = lv_obj_get_parent(card_value_owner);
        lv_obj_set_grid_cell(card, LV_GRID_ALIGN_STRETCH, col, col_span, LV_GRID_ALIGN_STRETCH, row, 1);
    };

    lbl_diag_tint   = make_diag_card(grid, "T internal", lv_color_hex(0x4FC3F7));
    place(lbl_diag_tint, 0, 1, 0);
    lbl_diag_tboost = make_diag_card(grid, "T boost out", lv_color_hex(0x4FC3F7));
    place(lbl_diag_tboost, 1, 1, 0);
    lbl_diag_flow   = make_diag_card(grid, "Flow", lv_color_hex(0x81C784));
    place(lbl_diag_flow, 2, 1, 0);
    lbl_diag_power  = make_diag_card(grid, "Power", lv_color_hex(0xFFB74D));
    place(lbl_diag_power, 0, 1, 1);
    lbl_diag_plc    = make_diag_card(grid, "Communication", lv_color_hex(0xE57373));
    place(lbl_diag_plc, 1, 1, 1);
    lbl_diag_heater_int   = make_diag_card(grid, "Heater Internal", lv_color_hex(0xB0BEC5));
    place(lbl_diag_heater_int, 2, 1, 1);
    lbl_diag_heater_boost = make_diag_card(grid, "Heater Boost", lv_color_hex(0xB0BEC5));
    place(lbl_diag_heater_boost, 0, 1, 2);
    lbl_diag_rssi   = make_diag_card(grid, "WiFi RSSI", lv_color_hex(0xB0BEC5));
    place(lbl_diag_rssi, 1, 1, 2);
    lbl_diag_heap   = make_diag_card(grid, "Free memory", lv_color_hex(0xB0BEC5));
    place(lbl_diag_heap, 2, 1, 2);
    lbl_diag_uptime = make_diag_card(grid, "Uptime", lv_color_hex(0xB0BEC5));
    place(lbl_diag_uptime, 0, 3, 3);
}
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
