AmitParan/smart-boiler/master/src/ui/ui_manager.h

#ifndef UI_MANAGER_H
#define UI_MANAGER_H

void UI_Init();
void UI_UpdateWaterTemp(float value);
void UI_UpdateWeather(float temp, const char* condition);
void UI_SetBoilerState(bool is_on);
void UI_SetHeatingStatus(bool is_heating);
void UI_UpdateTime(int hour, int minute);
void UI_UpdateDate(const char* date_str);
void UI_UpdateWiFiStatus();
void fetchWeather();
void fetchSolarForecast();
void checkScreensaver();

// Extended home screen updates (all live packet fields)
void UI_UpdateBoostTemp(float value);
void UI_UpdateFlowRate(float value);
void UI_UpdateSystemMode(const char* mode);
void UI_UpdateSSRStatus(bool internal_on, bool boost_on);
void UI_UpdateSensorData(float t_internal, float t_boost, float flow, float power_w);
void UI_UpdatePLCStatus(bool connected);

// --- Smart-preheat interface (reads the Schedule-page operation mode) ---
#include <stdint.h>
uint8_t  UI_GetOpMode();         // 0=DUMB (auto off), 1=READY_BY, 2=SMART
uint8_t  UI_GetReadyByMinutes(uint16_t* out, uint8_t maxN);  // enabled ready-by times today; returns count
uint8_t  UI_GetHouseholdSize();  // number of people (1..8)

#endif
